Occator/DripMatic/src/ff.c

/*----------------------------------------------------------------------------/
/  FatFs - Generic FAT Filesystem Module  R0.13b                              /
/-----------------------------------------------------------------------------/
/
/ Copyright (C) 2018, ChaN, all right reserved.
/
/ FatFs module is an open source software. Redistribution and use of FatFs in
/ source and binary forms, with or without modification, are permitted provided
/ that the following condition is met:
/
/ 1. Redistributions of source code must retain the above copyright notice,
/    this condition and the following disclaimer.
/
/ This software is provided by the copyright holder and contributors "AS IS"
/ and any warranties related to this software are DISCLAIMED.
/ The copyright owner or contributors be NOT LIABLE for any damages caused
/ by use of this software.
/
/----------------------------------------------------------------------------*/


#include "ff.h"			/* Declarations of FatFs API */
#include "diskio.h"		/* Declarations of device I/O functions */

/*--------------------------------------------------------------------------
own includings
/----------------------------------------------------------------------------*/
#include "rtc_3w.h"

/*--------------------------------------------------------------------------

   Module Private Definitions

---------------------------------------------------------------------------*/

#if FF_DEFINED != 63463	/* Revision ID */
#error Wrong include file (ff.h).
#endif

extern "C"
{

/* Character code support macros */
#define IsUpper(c)		((c) >= 'A' && (c) <= 'Z')
#define IsLower(c)		((c) >= 'a' && (c) <= 'z')
#define IsDigit(c)		((c) >= '0' && (c) <= '9')
#define IsSurrogate(c)	((c) >= 0xD800 && (c) <= 0xDFFF)
#define IsSurrogateH(c)	((c) >= 0xD800 && (c) <= 0xDBFF)
#define IsSurrogateL(c)	((c) >= 0xDC00 && (c) <= 0xDFFF)


/* Additional file attribute bits for internal use */
#define AM_VOL		0x08	/* Volume label */
#define AM_LFN		0x0F	/* LFN entry */
#define AM_MASK		0x3F	/* Mask of defined bits */


/* Additional file access control and file status flags for internal use */
#define FA_SEEKEND	0x20	/* Seek to end of the file on file open */
#define FA_MODIFIED	0x40	/* File has been modified */
#define FA_DIRTY	0x80	/* FIL.buf[] needs to be written-back */


/* Name status flags in fn[11] */
#define NSFLAG		11		/* Index of the name status byte */
#define NS_LOSS		0x01	/* Out of 8.3 format */
#define NS_LFN		0x02	/* Force to create LFN entry */
#define NS_LAST		0x04	/* Last segment */
#define NS_BODY		0x08	/* Lower case flag (body) */
#define NS_EXT		0x10	/* Lower case flag (ext) */
#define NS_DOT		0x20	/* Dot entry */
#define NS_NOLFN	0x40	/* Do not find LFN */
#define NS_NONAME	0x80	/* Not followed */


/* Limits and boundaries */
#define MAX_DIR		0x200000		/* Max size of FAT directory */
#define MAX_DIR_EX	0x10000000		/* Max size of exFAT directory */
#define MAX_FAT12	0xFF5			/* Max FAT12 clusters (differs from specs, but right for real DOS/Windows behavior) */
#define MAX_FAT16	0xFFF5			/* Max FAT16 clusters (differs from specs, but right for real DOS/Windows behavior) */
#define MAX_FAT32	0x0FFFFFF5		/* Max FAT32 clusters (not specified, practical limit) */
#define MAX_EXFAT	0x7FFFFFFD		/* Max exFAT clusters (differs from specs, implementation limit) */


/* FatFs refers the FAT structure as simple byte array instead of structure member
/ because the C structure is not binary compatible between different platforms */

#define BS_JmpBoot			0		/* x86 jump instruction (3-byte) */
#define BS_OEMName			3		/* OEM name (8-byte) */
#define BPB_BytsPerSec		11		/* Sector size [byte] (WORD) */
#define BPB_SecPerClus		13		/* Cluster size [sector] (BYTE) */
#define BPB_RsvdSecCnt		14		/* Size of reserved area [sector] (WORD) */
#define BPB_NumFATs			16		/* Number of FATs (BYTE) */
#define BPB_RootEntCnt		17		/* Size of root directory area for FAT [entry] (WORD) */
#define BPB_TotSec16		19		/* Volume size (16-bit) [sector] (WORD) */
#define BPB_Media			21		/* Media descriptor byte (BYTE) */
#define BPB_FATSz16			22		/* FAT size (16-bit) [sector] (WORD) */
#define BPB_SecPerTrk		24		/* Number of sectors per track for int13h [sector] (WORD) */
#define BPB_NumHeads		26		/* Number of heads for int13h (WORD) */
#define BPB_HiddSec			28		/* Volume offset from top of the drive (DWORD) */
#define BPB_TotSec32		32		/* Volume size (32-bit) [sector] (DWORD) */
#define BS_DrvNum			36		/* Physical drive number for int13h (BYTE) */
#define BS_NTres			37		/* WindowsNT error flag (BYTE) */
#define BS_BootSig			38		/* Extended boot signature (BYTE) */
#define BS_VolID			39		/* Volume serial number (DWORD) */
#define BS_VolLab			43		/* Volume label string (8-byte) */
#define BS_FilSysType		54		/* Filesystem type string (8-byte) */
#define BS_BootCode			62		/* Boot code (448-byte) */
#define BS_55AA				510		/* Signature word (WORD) */

#define BPB_FATSz32			36		/* FAT32: FAT size [sector] (DWORD) */
#define BPB_ExtFlags32		40		/* FAT32: Extended flags (WORD) */
#define BPB_FSVer32			42		/* FAT32: Filesystem version (WORD) */
#define BPB_RootClus32		44		/* FAT32: Root directory cluster (DWORD) */
#define BPB_FSInfo32		48		/* FAT32: Offset of FSINFO sector (WORD) */
#define BPB_BkBootSec32		50		/* FAT32: Offset of backup boot sector (WORD) */
#define BS_DrvNum32			64		/* FAT32: Physical drive number for int13h (BYTE) */
#define BS_NTres32			65		/* FAT32: Error flag (BYTE) */
#define BS_BootSig32		66		/* FAT32: Extended boot signature (BYTE) */
#define BS_VolID32			67		/* FAT32: Volume serial number (DWORD) */
#define BS_VolLab32			71		/* FAT32: Volume label string (8-byte) */
#define BS_FilSysType32		82		/* FAT32: Filesystem type string (8-byte) */
#define BS_BootCode32		90		/* FAT32: Boot code (420-byte) */

#define BPB_ZeroedEx		11		/* exFAT: MBZ field (53-byte) */
#define BPB_VolOfsEx		64		/* exFAT: Volume offset from top of the drive [sector] (QWORD) */
#define BPB_TotSecEx		72		/* exFAT: Volume size [sector] (QWORD) */
#define BPB_FatOfsEx		80		/* exFAT: FAT offset from top of the volume [sector] (DWORD) */
#define BPB_FatSzEx			84		/* exFAT: FAT size [sector] (DWORD) */
#define BPB_DataOfsEx		88		/* exFAT: Data offset from top of the volume [sector] (DWORD) */
#define BPB_NumClusEx		92		/* exFAT: Number of clusters (DWORD) */
#define BPB_RootClusEx		96		/* exFAT: Root directory start cluster (DWORD) */
#define BPB_VolIDEx			100		/* exFAT: Volume serial number (DWORD) */
#define BPB_FSVerEx			104		/* exFAT: Filesystem version (WORD) */
#define BPB_VolFlagEx		106		/* exFAT: Volume flags (WORD) */
#define BPB_BytsPerSecEx	108		/* exFAT: Log2 of sector size in unit of byte (BYTE) */
#define BPB_SecPerClusEx	109		/* exFAT: Log2 of cluster size in unit of sector (BYTE) */
#define BPB_NumFATsEx		110		/* exFAT: Number of FATs (BYTE) */
#define BPB_DrvNumEx		111		/* exFAT: Physical drive number for int13h (BYTE) */
#define BPB_PercInUseEx		112		/* exFAT: Percent in use (BYTE) */
#define BPB_RsvdEx			113		/* exFAT: Reserved (7-byte) */
#define BS_BootCodeEx		120		/* exFAT: Boot code (390-byte) */

#define DIR_Name			0		/* Short file name (11-byte) */
#define DIR_Attr			11		/* Attribute (BYTE) */
#define DIR_NTres			12		/* Lower case flag (BYTE) */
#define DIR_CrtTime10		13		/* Created time sub-second (BYTE) */
#define DIR_CrtTime			14		/* Created time (DWORD) */
#define DIR_LstAccDate		18		/* Last accessed date (WORD) */
#define DIR_FstClusHI		20		/* Higher 16-bit of first cluster (WORD) */
#define DIR_ModTime			22		/* Modified time (DWORD) */
#define DIR_FstClusLO		26		/* Lower 16-bit of first cluster (WORD) */
#define DIR_FileSize		28		/* File size (DWORD) */
#define LDIR_Ord			0		/* LFN: LFN order and LLE flag (BYTE) */
#define LDIR_Attr			11		/* LFN: LFN attribute (BYTE) */
#define LDIR_Type			12		/* LFN: Entry type (BYTE) */
#define LDIR_Chksum			13		/* LFN: Checksum of the SFN (BYTE) */
#define LDIR_FstClusLO		26		/* LFN: MBZ field (WORD) */
#define XDIR_Type			0		/* exFAT: Type of exFAT directory entry (BYTE) */
#define XDIR_NumLabel		1		/* exFAT: Number of volume label characters (BYTE) */
#define XDIR_Label			2		/* exFAT: Volume label (11-WORD) */
#define XDIR_CaseSum		4		/* exFAT: Sum of case conversion table (DWORD) */
#define XDIR_NumSec			1		/* exFAT: Number of secondary entries (BYTE) */
#define XDIR_SetSum			2		/* exFAT: Sum of the set of directory entries (WORD) */
#define XDIR_Attr			4		/* exFAT: File attribute (WORD) */
#define XDIR_CrtTime		8		/* exFAT: Created time (DWORD) */
#define XDIR_ModTime		12		/* exFAT: Modified time (DWORD) */
#define XDIR_AccTime		16		/* exFAT: Last accessed time (DWORD) */
#define XDIR_CrtTime10		20		/* exFAT: Created time subsecond (BYTE) */
#define XDIR_ModTime10		21		/* exFAT: Modified time subsecond (BYTE) */
#define XDIR_CrtTZ			22		/* exFAT: Created timezone (BYTE) */
#define XDIR_ModTZ			23		/* exFAT: Modified timezone (BYTE) */
#define XDIR_AccTZ			24		/* exFAT: Last accessed timezone (BYTE) */
#define XDIR_GenFlags		33		/* exFAT: General secondary flags (BYTE) */
#define XDIR_NumName		35		/* exFAT: Number of file name characters (BYTE) */
#define XDIR_NameHash		36		/* exFAT: Hash of file name (WORD) */
#define XDIR_ValidFileSize	40		/* exFAT: Valid file size (QWORD) */
#define XDIR_FstClus		52		/* exFAT: First cluster of the file data (DWORD) */
#define XDIR_FileSize		56		/* exFAT: File/Directory size (QWORD) */

#define SZDIRE				32		/* Size of a directory entry */
#define DDEM				0xE5	/* Deleted directory entry mark set to DIR_Name[0] */
#define RDDEM				0x05	/* Replacement of the character collides with DDEM */
#define LLEF				0x40	/* Last long entry flag in LDIR_Ord */

#define FSI_LeadSig			0		/* FAT32 FSI: Leading signature (DWORD) */
#define FSI_StrucSig		484		/* FAT32 FSI: Structure signature (DWORD) */
#define FSI_Free_Count		488		/* FAT32 FSI: Number of free clusters (DWORD) */
#define FSI_Nxt_Free		492		/* FAT32 FSI: Last allocated cluster (DWORD) */

#define MBR_Table			446		/* MBR: Offset of partition table in the MBR */
#define SZ_PTE				16		/* MBR: Size of a partition table entry */
#define PTE_Boot			0		/* MBR PTE: Boot indicator */
#define PTE_StHead			1		/* MBR PTE: Start head */
#define PTE_StSec			2		/* MBR PTE: Start sector */
#define PTE_StCyl			3		/* MBR PTE: Start cylinder */
#define PTE_System			4		/* MBR PTE: System ID */
#define PTE_EdHead			5		/* MBR PTE: End head */
#define PTE_EdSec			6		/* MBR PTE: End sector */
#define PTE_EdCyl			7		/* MBR PTE: End cylinder */
#define PTE_StLba			8		/* MBR PTE: Start in LBA */
#define PTE_SizLba			12		/* MBR PTE: Size in LBA */


/* Post process on fatal error in the file operations */
#define ABORT(fs, res)		{ fp->err = (BYTE)(res); LEAVE_FF(fs, res); }


/* Re-entrancy related */
#if FF_FS_REENTRANT
#if FF_USE_LFN == 1
#error Static LFN work area cannot be used at thread-safe configuration
#endif
#define LEAVE_FF(fs, res)	{ unlock_fs(fs, res); return res; }
#else
#define LEAVE_FF(fs, res)	return res
#endif


/* Definitions of volume - physical location conversion */
#if FF_MULTI_PARTITION
#define LD2PD(vol) VolToPart[vol].pd	/* Get physical drive number */
#define LD2PT(vol) VolToPart[vol].pt	/* Get partition index */
#else
#define LD2PD(vol) (BYTE)(vol)	/* Each logical drive is bound to the same physical drive number */
#define LD2PT(vol) 0			/* Find first valid partition or in SFD */
#endif


/* Definitions of sector size */
#if (FF_MAX_SS < FF_MIN_SS) || (FF_MAX_SS != 512 && FF_MAX_SS != 1024 && FF_MAX_SS != 2048 && FF_MAX_SS != 4096) || (FF_MIN_SS != 512 && FF_MIN_SS != 1024 && FF_MIN_SS != 2048 && FF_MIN_SS != 4096)
#error Wrong sector size configuration
#endif
#if FF_MAX_SS == FF_MIN_SS
#define SS(fs)	((UINT)FF_MAX_SS)	/* Fixed sector size */
#else
#define SS(fs)	((fs)->ssize)	/* Variable sector size */
#endif


/* Timestamp */
#if FF_FS_NORTC == 1
#if FF_NORTC_YEAR < 1980 || FF_NORTC_YEAR > 2107 || FF_NORTC_MON < 1 || FF_NORTC_MON > 12 || FF_NORTC_MDAY < 1 || FF_NORTC_MDAY > 31
#error Invalid FF_FS_NORTC settings
#endif
#define GET_FATTIME()	((DWORD)(FF_NORTC_YEAR - 1980) << 25 | (DWORD)FF_NORTC_MON << 21 | (DWORD)FF_NORTC_MDAY << 16)
#else
#define GET_FATTIME()	get_fattime()
#endif


/* File lock controls */
#if FF_FS_LOCK != 0
#if FF_FS_READONLY
#error FF_FS_LOCK must be 0 at read-only configuration
#endif
typedef struct {
	FATFS *fs;		/* Object ID 1, volume (NULL:blank entry) */
	DWORD clu;		/* Object ID 2, containing directory (0:root) */
	DWORD ofs;		/* Object ID 3, offset in the directory */
	WORD ctr;		/* Object open counter, 0:none, 0x01..0xFF:read mode open count, 0x100:write mode */
} FILESEM;
#endif


/* SBCS up-case tables (\x80-\xFF) */
#define TBL_CT437  {0x80,0x9A,0x45,0x41,0x8E,0x41,0x8F,0x80,0x45,0x45,0x45,0x49,0x49,0x49,0x8E,0x8F, \
					0x90,0x92,0x92,0x4F,0x99,0x4F,0x55,0x55,0x59,0x99,0x9A,0x9B,0x9C,0x9D,0x9E,0x9F, \
					0x41,0x49,0x4F,0x55,0xA5,0xA5,0xA6,0xA7,0xA8,0xA9,0xAA,0xAB,0xAC,0xAD,0xAE,0xAF, \
					0xB0,0xB1,0xB2,0xB3,0xB4,0xB5,0xB6,0xB7,0xB8,0xB9,0xBA,0xBB,0xBC,0xBD,0xBE,0xBF, \
					0xC0,0xC1,0xC2,0xC3,0xC4,0xC5,0xC6,0xC7,0xC8,0xC9,0xCA,0xCB,0xCC,0xCD,0xCE,0xCF, \
					0xD0,0xD1,0xD2,0xD3,0xD4,0xD5,0xD6,0xD7,0xD8,0xD9,0xDA,0xDB,0xDC,0xDD,0xDE,0xDF, \
					0xE0,0xE1,0xE2,0xE3,0xE4,0xE5,0xE6,0xE7,0xE8,0xE9,0xEA,0xEB,0xEC,0xED,0xEE,0xEF, \
					0xF0,0xF1,0xF2,0xF3,0xF4,0xF5,0xF6,0xF7,0xF8,0xF9,0xFA,0xFB,0xFC,0xFD,0xFE,0xFF}
#define TBL_CT720  {0x80,0x81,0x82,0x83,0x84,0x85,0x86,0x87,0x88,0x89,0x8A,0x8B,0x8C,0x8D,0x8E,0x8F, \
					0x90,0x91,0x92,0x93,0x94,0x95,0x96,0x97,0x98,0x99,0x9A,0x9B,0x9C,0x9D,0x9E,0x9F, \
					0xA0,0xA1,0xA2,0xA3,0xA4,0xA5,0xA6,0xA7,0xA8,0xA9,0xAA,0xAB,0xAC,0xAD,0xAE,0xAF, \
					0xB0,0xB1,0xB2,0xB3,0xB4,0xB5,0xB6,0xB7,0xB8,0xB9,0xBA,0xBB,0xBC,0xBD,0xBE,0xBF, \
					0xC0,0xC1,0xC2,0xC3,0xC4,0xC5,0xC6,0xC7,0xC8,0xC9,0xCA,0xCB,0xCC,0xCD,0xCE,0xCF, \
					0xD0,0xD1,0xD2,0xD3,0xD4,0xD5,0xD6,0xD7,0xD8,0xD9,0xDA,0xDB,0xDC,0xDD,0xDE,0xDF, \
					0xE0,0xE1,0xE2,0xE3,0xE4,0xE5,0xE6,0xE7,0xE8,0xE9,0xEA,0xEB,0xEC,0xED,0xEE,0xEF, \
					0xF0,0xF1,0xF2,0xF3,0xF4,0xF5,0xF6,0xF7,0xF8,0xF9,0xFA,0xFB,0xFC,0xFD,0xFE,0xFF}
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
#define TBL_CT869  {0x80,0x81,0x82,0x83,0x84,0x85,0x86,0x87,0x88,0x89,0x8A,0x8B,0x8C,0x8D,0x8E,0x8F, \
					0x90,0x91,0x92,0x93,0x94,0x95,0x96,0x97,0x98,0x99,0x9A,0x86,0x9C,0x8D,0x8F,0x90, \
					0x91,0x90,0x92,0x95,0xA4,0xA5,0xA6,0xA7,0xA8,0xA9,0xAA,0xAB,0xAC,0xAD,0xAE,0xAF, \
					0xB0,0xB1,0xB2,0xB3,0xB4,0xB5,0xB6,0xB7,0xB8,0xB9,0xBA,0xBB,0xBC,0xBD,0xBE,0xBF, \
					0xC0,0xC1,0xC2,0xC3,0xC4,0xC5,0xC6,0xC7,0xC8,0xC9,0xCA,0xCB,0xCC,0xCD,0xCE,0xCF, \
					0xD0,0xD1,0xD2,0xD3,0xD4,0xD5,0xA4,0xA5,0xA6,0xD9,0xDA,0xDB,0xDC,0xA7,0xA8,0xDF, \
					0xA9,0xAA,0xAC,0xAD,0xB5,0xB6,0xB7,0xB8,0xBD,0xBE,0xC6,0xC7,0xCF,0xCF,0xD0,0xEF, \
					0xF0,0xF1,0xD1,0xD2,0xD3,0xF5,0xD4,0xF7,0xF8,0xF9,0xD5,0x96,0x95,0x98,0xFE,0xFF}


/* DBCS code range |----- 1st byte -----|  |----------- 2nd byte -----------| */
#define TBL_DC932 {0x81, 0x9F, 0xE0, 0xFC, 0x40, 0x7E, 0x80, 0xFC, 0x00, 0x00}
#define TBL_DC936 {0x81, 0xFE, 0x00, 0x00, 0x40, 0x7E, 0x80, 0xFE, 0x00, 0x00}
#define TBL_DC949 {0x81, 0xFE, 0x00, 0x00, 0x41, 0x5A, 0x61, 0x7A, 0x81, 0xFE}
#define TBL_DC950 {0x81, 0xFE, 0x00, 0x00, 0x40, 0x7E, 0xA1, 0xFE, 0x00, 0x00}


/* Macros for table definitions */
#define MERGE_2STR(a, b) a ## b
#define MKCVTBL(hd, cp) MERGE_2STR(hd, cp)




/*--------------------------------------------------------------------------

   Module Private Work Area

---------------------------------------------------------------------------*/
/* Remark: Variables defined here without initial value shall be guaranteed
/  zero/null at start-up. If not, the linker option or start-up routine is
/  not compliance with C standard. */

/*--------------------------------*/
/* File/Volume controls           */
/*--------------------------------*/

#if FF_VOLUMES < 1 || FF_VOLUMES > 10
#error Wrong FF_VOLUMES setting
#endif
static FATFS* FatFs[FF_VOLUMES];	/* Pointer to the filesystem objects (logical drives) */
static WORD Fsid;					/* Filesystem mount ID */

#if FF_FS_RPATH != 0
static BYTE CurrVol;				/* Current drive */
#endif

#if FF_FS_LOCK != 0
static FILESEM Files[FF_FS_LOCK];	/* Open object lock semaphores */
#endif

#if FF_STR_VOLUME_ID
#ifdef FF_VOLUME_STRS
static const char* const VolumeStr[FF_VOLUMES] = {FF_VOLUME_STRS};	/* Pre-defined volume ID */
#endif
#endif


/*--------------------------------*/
/* LFN/Directory working buffer   */
/*--------------------------------*/

#if FF_USE_LFN == 0		/* Non-LFN configuration */
#if FF_FS_EXFAT
#error LFN must be enabled when enable exFAT
#endif
#define DEF_NAMBUF
#define INIT_NAMBUF(fs)
#define FREE_NAMBUF()
#define LEAVE_MKFS(res)	return res

#else					/* LFN configurations */
#if FF_MAX_LFN < 12 || FF_MAX_LFN > 255
#error Wrong setting of FF_MAX_LFN
#endif
#if FF_LFN_BUF < FF_SFN_BUF || FF_SFN_BUF < 12
#error Wrong setting of FF_LFN_BUF or FF_SFN_BUF
#endif
#if FF_LFN_UNICODE < 0 || FF_LFN_UNICODE > 3
#error Wrong setting of FF_LFN_UNICODE
#endif
static const BYTE LfnOfs[] = {1,3,5,7,9,14,16,18,20,22,24,28,30};	/* FAT: Offset of LFN characters in the directory entry */
#define MAXDIRB(nc)	((nc + 44U) / 15 * SZDIRE)	/* exFAT: Size of directory entry block scratchpad buffer needed for the name length */

#if FF_USE_LFN == 1		/* LFN enabled with static working buffer */
#if FF_FS_EXFAT
static BYTE	DirBuf[MAXDIRB(FF_MAX_LFN)];	/* Directory entry block scratchpad buffer */
#endif
static WCHAR LfnBuf[FF_MAX_LFN + 1];		/* LFN working buffer */
#define DEF_NAMBUF
#define INIT_NAMBUF(fs)
#define FREE_NAMBUF()
#define LEAVE_MKFS(res)	return res

#elif FF_USE_LFN == 2 	/* LFN enabled with dynamic working buffer on the stack */
#if FF_FS_EXFAT
#define DEF_NAMBUF		WCHAR lbuf[FF_MAX_LFN+1]; BYTE dbuf[MAXDIRB(FF_MAX_LFN)];	/* LFN working buffer and directory entry block scratchpad buffer */
#define INIT_NAMBUF(fs)	{ (fs)->lfnbuf = lbuf; (fs)->dirbuf = dbuf; }
#define FREE_NAMBUF()
#else
#define DEF_NAMBUF		WCHAR lbuf[FF_MAX_LFN+1];	/* LFN working buffer */
#define INIT_NAMBUF(fs)	{ (fs)->lfnbuf = lbuf; }
#define FREE_NAMBUF()
#endif
#define LEAVE_MKFS(res)	return res

#elif FF_USE_LFN == 3 	/* LFN enabled with dynamic working buffer on the heap */
#if FF_FS_EXFAT
#define DEF_NAMBUF		WCHAR *lfn;	/* Pointer to LFN working buffer and directory entry block scratchpad buffer */
#define INIT_NAMBUF(fs)	{ lfn = ff_memalloc((FF_MAX_LFN+1)*2 + MAXDIRB(FF_MAX_LFN)); if (!lfn) LEAVE_FF(fs, FR_NOT_ENOUGH_CORE); (fs)->lfnbuf = lfn; (fs)->dirbuf = (BYTE*)(lfn+FF_MAX_LFN+1); }
#define FREE_NAMBUF()	ff_memfree(lfn)
#else
#define DEF_NAMBUF		WCHAR *lfn;	/* Pointer to LFN working buffer */
#define INIT_NAMBUF(fs)	{ lfn = ff_memalloc((FF_MAX_LFN+1)*2); if (!lfn) LEAVE_FF(fs, FR_NOT_ENOUGH_CORE); (fs)->lfnbuf = lfn; }
#define FREE_NAMBUF()	ff_memfree(lfn)
#endif
#define LEAVE_MKFS(res)	{ if (!work) ff_memfree(buf); return res; }
#define MAX_MALLOC	0x8000	/* Must be >=FF_MAX_SS */

#else
#error Wrong setting of FF_USE_LFN

#endif	/* FF_USE_LFN == 1 */
#endif	/* FF_USE_LFN == 0 */



/*--------------------------------*/
/* Code conversion tables         */
/*--------------------------------*/

#if FF_CODE_PAGE == 0		/* Run-time code page configuration */
#define CODEPAGE CodePage
static WORD CodePage;	/* Current code page */
static const BYTE *ExCvt, *DbcTbl;	/* Pointer to current SBCS up-case table and DBCS code range table below */
static const BYTE Ct437[] = TBL_CT437;
static const BYTE Ct720[] = TBL_CT720;
static const BYTE Ct737[] = TBL_CT737;
static const BYTE Ct771[] = TBL_CT771;
static const BYTE Ct775[] = TBL_CT775;
static const BYTE Ct850[] = TBL_CT850;
static const BYTE Ct852[] = TBL_CT852;
static const BYTE Ct855[] = TBL_CT855;
static const BYTE Ct857[] = TBL_CT857;
static const BYTE Ct860[] = TBL_CT860;
static const BYTE Ct861[] = TBL_CT861;
static const BYTE Ct862[] = TBL_CT862;
static const BYTE Ct863[] = TBL_CT863;
static const BYTE Ct864[] = TBL_CT864;
static const BYTE Ct865[] = TBL_CT865;
static const BYTE Ct866[] = TBL_CT866;
static const BYTE Ct869[] = TBL_CT869;
static const BYTE Dc932[] = TBL_DC932;
static const BYTE Dc936[] = TBL_DC936;
static const BYTE Dc949[] = TBL_DC949;
static const BYTE Dc950[] = TBL_DC950;

#elif FF_CODE_PAGE < 900	/* Static code page configuration (SBCS) */
#define CODEPAGE FF_CODE_PAGE
static const BYTE ExCvt[] = MKCVTBL(TBL_CT, FF_CODE_PAGE);

#else					/* Static code page configuration (DBCS) */
#define CODEPAGE FF_CODE_PAGE
static const BYTE DbcTbl[] = MKCVTBL(TBL_DC, FF_CODE_PAGE);

#endif




/*--------------------------------------------------------------------------

   Module Private Functions

---------------------------------------------------------------------------*/

/*-----------------------------------------------------------------------*/
/* RTC-Module get_fattime implementation                       */
/*-----------------------------------------------------------------------*/
DWORD get_fattime()
{

	cDeviceRTC::GetInstance().update_rtcTime();
	return ( (DWORD)(cDeviceRTC::GetInstance().rtcTime.year - 1980) << 25)
					| ( (DWORD)cDeviceRTC::GetInstance().rtcTime.month << 21)
					| ( (DWORD)cDeviceRTC::GetInstance().rtcTime.date << 16)
					| ( (DWORD)(cDeviceRTC::GetInstance().rtcTime.hours - 2) << 11)
					| ( (DWORD)cDeviceRTC::GetInstance().rtcTime.minutes << 5)
					| ( (DWORD)cDeviceRTC::GetInstance().rtcTime.seconds >> 1);
}

/*-----------------------------------------------------------------------*/
/* Load/Store multi-byte word in the FAT structure                       */
/*-----------------------------------------------------------------------*/

static WORD ld_word (const BYTE* ptr)	/*	 Load a 2-byte little-endian word */
{
	WORD rv;

	rv = ptr[1];
	rv = rv << 8 | ptr[0];
	return rv;
}

static DWORD ld_dword (const BYTE* ptr)	/* Load a 4-byte little-endian word */
{
	DWORD rv;

	rv = ptr[3];
	rv = rv << 8 | ptr[2];
	rv = rv << 8 | ptr[1];
	rv = rv << 8 | ptr[0];
	return rv;
}

#if FF_FS_EXFAT
static QWORD ld_qword (const BYTE* ptr)	/* Load an 8-byte little-endian word */
{
	QWORD rv;

	rv = ptr[7];
	rv = rv << 8 | ptr[6];
	rv = rv << 8 | ptr[5];
	rv = rv << 8 | ptr[4];
	rv = rv << 8 | ptr[3];
	rv = rv << 8 | ptr[2];
	rv = rv << 8 | ptr[1];
	rv = rv << 8 | ptr[0];
	return rv;
}
#endif

#if !FF_FS_READONLY
static void st_word (BYTE* ptr, WORD val)	/* Store a 2-byte word in little-endian */
{
	*ptr++ = (BYTE)val; val >>= 8;
	*ptr++ = (BYTE)val;
}

static void st_dword (BYTE* ptr, DWORD val)	/* Store a 4-byte word in little-endian */
{
	*ptr++ = (BYTE)val; val >>= 8;
	*ptr++ = (BYTE)val; val >>= 8;
	*ptr++ = (BYTE)val; val >>= 8;
	*ptr++ = (BYTE)val;
}

#if FF_FS_EXFAT
static void st_qword (BYTE* ptr, QWORD val)	/* Store an 8-byte word in little-endian */
{
	*ptr++ = (BYTE)val; val >>= 8;
	*ptr++ = (BYTE)val; val >>= 8;
	*ptr++ = (BYTE)val; val >>= 8;
	*ptr++ = (BYTE)val; val >>= 8;
	*ptr++ = (BYTE)val; val >>= 8;
	*ptr++ = (BYTE)val; val >>= 8;
	*ptr++ = (BYTE)val; val >>= 8;
	*ptr++ = (BYTE)val;
}
#endif
#endif	/* !FF_FS_READONLY */



/*-----------------------------------------------------------------------*/
/* String functions                                                      */
/*-----------------------------------------------------------------------*/

/* Copy memory to memory */
static void mem_cpy (void* dst, const void* src, UINT cnt)
{
	BYTE *d = (BYTE*)dst;
	const BYTE *s = (const BYTE*)src;

	if (cnt != 0) {
		do {
			*d++ = *s++;
		} while (--cnt);
	}
}


/* Fill memory block */
static void mem_set (void* dst, int val, UINT cnt)
{
	BYTE *d = (BYTE*)dst;

	do {
		*d++ = (BYTE)val;
	} while (--cnt);
}


/* Compare memory block */
static int mem_cmp (const void* dst, const void* src, UINT cnt)	/* ZR:same, NZ:different */
{
	const BYTE *d = (const BYTE *)dst, *s = (const BYTE *)src;
	int r = 0;

	do {
		r = *d++ - *s++;
	} while (--cnt && r == 0);

	return r;
}


/* Check if chr is contained in the string */
static int chk_chr (const char* str, int chr)	/* NZ:contained, ZR:not contained */
{
	while (*str && *str != chr) str++;
	return *str;
}


/* Test if the character is DBC 1st byte */
static int dbc_1st (BYTE c)
{
#if FF_CODE_PAGE == 0		/* Variable code page */
	if (DbcTbl && c >= DbcTbl[0]) {
		if (c <= DbcTbl[1]) return 1;					/* 1st byte range 1 */
		if (c >= DbcTbl[2] && c <= DbcTbl[3]) return 1;	/* 1st byte range 2 */
	}
#elif FF_CODE_PAGE >= 900	/* DBCS fixed code page */
	if (c >= DbcTbl[0]) {
		if (c <= DbcTbl[1]) return 1;
		if (c >= DbcTbl[2] && c <= DbcTbl[3]) return 1;
	}
#else						/* SBCS fixed code page */
	if (c != 0) return 0;	/* Always false */
#endif
	return 0;
}


/* Test if the character is DBC 2nd byte */
static int dbc_2nd (BYTE c)
{
#if FF_CODE_PAGE == 0		/* Variable code page */
	if (DbcTbl && c >= DbcTbl[4]) {
		if (c <= DbcTbl[5]) return 1;					/* 2nd byte range 1 */
		if (c >= DbcTbl[6] && c <= DbcTbl[7]) return 1;	/* 2nd byte range 2 */
		if (c >= DbcTbl[8] && c <= DbcTbl[9]) return 1;	/* 2nd byte range 3 */
	}
#elif FF_CODE_PAGE >= 900	/* DBCS fixed code page */
	if (c >= DbcTbl[4]) {
		if (c <= DbcTbl[5]) return 1;
		if (c >= DbcTbl[6] && c <= DbcTbl[7]) return 1;
		if (c >= DbcTbl[8] && c <= DbcTbl[9]) return 1;
	}
#else						/* SBCS fixed code page */
	if (c != 0) return 0;	/* Always false */
#endif
	return 0;
}


#if FF_USE_LFN

/* Get a character from TCHAR string in defined API encodeing */
static DWORD tchar2uni (	/* Returns character in UTF-16 encoding (>=0x10000 on double encoding unit, 0xFFFFFFFF on decode error) */
	const TCHAR** str		/* Pointer to pointer to TCHAR string in configured encoding */
)
{
	DWORD uc;
	const TCHAR *p = *str;

#if FF_LFN_UNICODE == 1		/* UTF-16 input */
	WCHAR wc;

	uc = *p++;	/* Get a unit */
	if (IsSurrogate(uc)) {	/* Surrogate? */
		wc = *p++;		/* Get low surrogate */
		if (!IsSurrogateH(uc) || !IsSurrogateL(wc)) return 0xFFFFFFFF;	/* Wrong surrogate? */
		uc = uc << 16 | wc;
	}

#elif FF_LFN_UNICODE == 2	/* UTF-8 input */
	BYTE b;
	int nf;

	uc = (BYTE)*p++;	/* Get a unit */
	if (uc & 0x80) {	/* Multiple byte code? */
		if ((uc & 0xE0) == 0xC0) {	/* 2-byte sequence? */
			uc &= 0x1F; nf = 1;
		} else {
			if ((uc & 0xF0) == 0xE0) {	/* 3-byte sequence? */
				uc &= 0x0F; nf = 2;
			} else {
				if ((uc & 0xF8) == 0xF0) {	/* 4-byte sequence? */
					uc &= 0x07; nf = 3;
				} else {					/* Wrong sequence */
					return 0xFFFFFFFF;
				}
			}
		}
		do {	/* Get trailing bytes */
			b = (BYTE)*p++;
			if ((b & 0xC0) != 0x80) return 0xFFFFFFFF;	/* Wrong sequence? */
			uc = uc << 6 | (b & 0x3F);
		} while (--nf != 0);
		if (uc < 0x80 || IsSurrogate(uc) || uc >= 0x110000) return 0xFFFFFFFF;	/* Wrong code? */
		if (uc >= 0x010000) uc = 0xD800DC00 | ((uc - 0x10000) << 6 & 0x3FF0000) | (uc & 0x3FF);	/* Make a surrogate pair if needed */
	}

#elif FF_LFN_UNICODE == 3	/* UTF-32 input */
	uc = (TCHAR)*p++;	/* Get a unit */
	if (uc >= 0x110000) return 0xFFFFFFFF;	/* Wrong code? */
	if (uc >= 0x010000) uc = 0xD800DC00 | ((uc - 0x10000) << 6 & 0x3FF0000) | (uc & 0x3FF);	/* Make a surrogate pair if needed */

#else		/* ANSI/OEM input */
	BYTE b;
	WCHAR wc;

	wc = (BYTE)*p++;			/* Get a byte */
	if (dbc_1st((BYTE)wc)) {	/* Is it a DBC 1st byte? */
		b = (BYTE)*p++;			/* Get 2nd byte */
		if (!dbc_2nd(b)) return 0xFFFFFFFF;	/* Invalid code? */
		wc = (wc << 8) + b;		/* Make a DBC */
	}
	if (wc != 0) {
		wc = ff_oem2uni(wc, CODEPAGE);	/* ANSI/OEM ==> Unicode */
		if (wc == 0) return 0xFFFFFFFF;	/* Invalid code? */
	}
	uc = wc;

#endif
	*str = p;	/* Next read pointer */
	return uc;
}


/* Output a TCHAR string in defined API encoding */
static BYTE put_utf (	/* Returns number of encoding units written (0:buffer overflow or wrong encoding) */
	DWORD chr,	/* UTF-16 encoded character (Double encoding unit char if >=0x10000) */
	TCHAR* buf,	/* Output buffer */
	UINT szb	/* Size of the buffer */
)
{
#if FF_LFN_UNICODE == 1	/* UTF-16 output */
	WCHAR hs, wc;

	hs = (WCHAR)(chr >> 16);
	wc = (WCHAR)chr;
	if (hs == 0) {	/* Single encoding unit? */
		if (szb < 1 || IsSurrogate(wc)) return 0;	/* Buffer overflow or wrong code? */
		*buf = wc;
		return 1;
	}
	if (szb < 2 || !IsSurrogateH(hs) || !IsSurrogateL(wc)) return 0;	/* Buffer overflow or wrong surrogate? */
	*buf++ = hs;
	*buf++ = wc;
	return 2;

#elif FF_LFN_UNICODE == 2	/* UTF-8 output */
	DWORD hc;

	if (chr < 0x80) {	/* Single byte code? */
		if (szb < 1) return 0;	/* Buffer overflow? */
		*buf = (TCHAR)chr;
		return 1;
	}
	if (chr < 0x800) {	/* 2-byte sequence? */
		if (szb < 2) return 0;	/* Buffer overflow? */
		*buf++ = (TCHAR)(0xC0 | (chr >> 6 & 0x1F));
		*buf++ = (TCHAR)(0x80 | (chr >> 0 & 0x3F));
		return 2;
	}
	if (chr < 0x10000) {	/* 3-byte sequence? */
		if (szb < 3 || IsSurrogate(chr)) return 0;	/* Buffer overflow or wrong code? */
		*buf++ = (TCHAR)(0xE0 | (chr >> 12 & 0x0F));
		*buf++ = (TCHAR)(0x80 | (chr >> 6 & 0x3F));
		*buf++ = (TCHAR)(0x80 | (chr >> 0 & 0x3F));
		return 3;
	}
	/* 4-byte sequence */
	if (szb < 4) return 0;	/* Buffer overflow? */
	hc = ((chr & 0xFFFF0000) - 0xD8000000) >> 6;	/* Get high 10 bits */
	chr = (chr & 0xFFFF) - 0xDC00;					/* Get low 10 bits */
	if (hc >= 0x100000 || chr >= 0x400) return 0;	/* Wrong surrogate? */
	chr = (hc | chr) + 0x10000;
	*buf++ = (TCHAR)(0xF0 | (chr >> 18 & 0x07));
	*buf++ = (TCHAR)(0x80 | (chr >> 12 & 0x3F));
	*buf++ = (TCHAR)(0x80 | (chr >> 6 & 0x3F));
	*buf++ = (TCHAR)(0x80 | (chr >> 0 & 0x3F));
	return 4;

#elif FF_LFN_UNICODE == 3	/* UTF-32 output */
	DWORD hc;

	if (szb < 1) return 0;	/* Buffer overflow? */
	if (chr >= 0x10000) {	/* Out of BMP? */
		hc = ((chr & 0xFFFF0000) - 0xD8000000) >> 6;	/* Get high 10 bits */
		chr = (chr & 0xFFFF) - 0xDC00;					/* Get low 10 bits */
		if (hc >= 0x100000 || chr >= 0x400) return 0;	/* Wrong surrogate? */
		chr = (hc | chr) + 0x10000;
	}
	*buf++ = (TCHAR)chr;
	return 1;

#else						/* ANSI/OEM output */
	WCHAR wc;

	wc = ff_uni2oem(chr, CODEPAGE);
	if (wc >= 0x100) {	/* Is this a DBC? */
		if (szb < 2) return 0;
		*buf++ = (char)(wc >> 8);	/* Store DBC 1st byte */
		*buf++ = (TCHAR)wc;			/* Store DBC 2nd byte */
		return 2;
	}
	if (wc == 0 || szb < 1) return 0;	/* Invalid char or buffer overflow? */
	*buf++ = (TCHAR)wc;					/* Store the character */
	return 1;
#endif
}
#endif	/* FF_USE_LFN */


#if FF_FS_REENTRANT
/*-----------------------------------------------------------------------*/
/* Request/Release grant to access the volume                            */
/*-----------------------------------------------------------------------*/
static int lock_fs (		/* 1:Ok, 0:timeout */
	FATFS* fs		/* Filesystem object */
)
{
	return ff_req_grant(fs->sobj);
}


static void unlock_fs (
	FATFS* fs,		/* Filesystem object */
	FRESULT res		/* Result code to be returned */
)
{
	if (fs && res != FR_NOT_ENABLED && res != FR_INVALID_DRIVE && res != FR_TIMEOUT) {
		ff_rel_grant(fs->sobj);
	}
}

#endif



#if FF_FS_LOCK != 0
/*-----------------------------------------------------------------------*/
/* File lock control functions                                           */
/*-----------------------------------------------------------------------*/

static FRESULT chk_lock (	/* Check if the file can be accessed */
	DIR* dp,		/* Directory object pointing the file to be checked */
	int acc			/* Desired access type (0:Read mode open, 1:Write mode open, 2:Delete or rename) */
)
{
	UINT i, be;

	/* Search open object table for the object */
	be = 0;
	for (i = 0; i < FF_FS_LOCK; i++) {
		if (Files[i].fs) {	/* Existing entry */
			if (Files[i].fs == dp->obj.fs &&	 	/* Check if the object matches with an open object */
				Files[i].clu == dp->obj.sclust &&
				Files[i].ofs == dp->dptr) break;
		} else {			/* Blank entry */
			be = 1;
		}
	}
	if (i == FF_FS_LOCK) {	/* The object has not been opened */
		return (!be && acc != 2) ? FR_TOO_MANY_OPEN_FILES : FR_OK;	/* Is there a blank entry for new object? */
	}

	/* The object was opened. Reject any open against writing file and all write mode open */
	return (acc != 0 || Files[i].ctr == 0x100) ? FR_LOCKED : FR_OK;
}


static int enq_lock (void)	/* Check if an entry is available for a new object */
{
	UINT i;

	for (i = 0; i < FF_FS_LOCK && Files[i].fs; i++) ;
	return (i == FF_FS_LOCK) ? 0 : 1;
}


static UINT inc_lock (	/* Increment object open counter and returns its index (0:Internal error) */
	DIR* dp,	/* Directory object pointing the file to register or increment */
	int acc		/* Desired access (0:Read, 1:Write, 2:Delete/Rename) */
)
{
	UINT i;


	for (i = 0; i < FF_FS_LOCK; i++) {	/* Find the object */
		if (Files[i].fs == dp->obj.fs &&
			Files[i].clu == dp->obj.sclust &&
			Files[i].ofs == dp->dptr) break;
	}

	if (i == FF_FS_LOCK) {				/* Not opened. Register it as new. */
		for (i = 0; i < FF_FS_LOCK && Files[i].fs; i++) ;
		if (i == FF_FS_LOCK) return 0;	/* No free entry to register (int err) */
		Files[i].fs = dp->obj.fs;
		Files[i].clu = dp->obj.sclust;
		Files[i].ofs = dp->dptr;
		Files[i].ctr = 0;
	}

	if (acc >= 1 && Files[i].ctr) return 0;	/* Access violation (int err) */

	Files[i].ctr = acc ? 0x100 : Files[i].ctr + 1;	/* Set semaphore value */

	return i + 1;	/* Index number origin from 1 */
}


static FRESULT dec_lock (	/* Decrement object open counter */
	UINT i			/* Semaphore index (1..) */
)
{
	WORD n;
	FRESULT res;


	if (--i < FF_FS_LOCK) {	/* Index number origin from 0 */
		n = Files[i].ctr;
		if (n == 0x100) n = 0;		/* If write mode open, delete the entry */
		if (n > 0) n--;				/* Decrement read mode open count */
		Files[i].ctr = n;
		if (n == 0) Files[i].fs = 0;	/* Delete the entry if open count gets zero */
		res = FR_OK;
	} else {
		res = FR_INT_ERR;			/* Invalid index nunber */
	}
	return res;
}


static void clear_lock (	/* Clear lock entries of the volume */
	FATFS *fs
)
{
	UINT i;

	for (i = 0; i < FF_FS_LOCK; i++) {
		if (Files[i].fs == fs) Files[i].fs = 0;
	}
}

#endif	/* FF_FS_LOCK != 0 */



/*-----------------------------------------------------------------------*/
/* Move/Flush disk access window in the filesystem object                */
/*-----------------------------------------------------------------------*/
#if !FF_FS_READONLY
static FRESULT sync_window (	/* Returns FR_OK or FR_DISK_ERR */
	FATFS* fs			/* Filesystem object */
)
{
	FRESULT res = FR_OK;


	if (fs->wflag) {	/* Is the disk access window dirty */
		if (disk_write(fs->pdrv, fs->win, fs->winsect, 1) == RES_OK) {	/* Write back the window */
			fs->wflag = 0;	/* Clear window dirty flag */
			if (fs->winsect - fs->fatbase < fs->fsize) {	/* Is it in the 1st FAT? */
				if (fs->n_fats == 2) disk_write(fs->pdrv, fs->win, fs->winsect + fs->fsize, 1);	/* Reflect it to 2nd FAT if needed */
			}
		} else {
			res = FR_DISK_ERR;
		}
	}
	return res;
}
#endif


static FRESULT move_window (	/* Returns FR_OK or FR_DISK_ERR */
	FATFS* fs,			/* Filesystem object */
	DWORD sector		/* Sector number to make appearance in the fs->win[] */
)
{
	FRESULT res = FR_OK;


	if (sector != fs->winsect) {	/* Window offset changed? */
#if !FF_FS_READONLY
		res = sync_window(fs);		/* Write-back changes */
#endif
		if (res == FR_OK) {			/* Fill sector window with new data */
			if (disk_read(fs->pdrv, fs->win, sector, 1) != RES_OK) {
				sector = 0xFFFFFFFF;	/* Invalidate window if read data is not valid */
				res = FR_DISK_ERR;
			}
			fs->winsect = sector;
		}
	}
	return res;
}




#if !FF_FS_READONLY
/*-----------------------------------------------------------------------*/
/* Synchronize filesystem and data on the storage                        */
/*-----------------------------------------------------------------------*/

static FRESULT sync_fs (	/* Returns FR_OK or FR_DISK_ERR */
	FATFS* fs		/* Filesystem object */
)
{
	FRESULT res;


	res = sync_window(fs);
	if (res == FR_OK) {
		if (fs->fs_type == FS_FAT32 && fs->fsi_flag == 1) {	/* FAT32: Update FSInfo sector if needed */
			/* Create FSInfo structure */
			mem_set(fs->win, 0, SS(fs));
			st_word(fs->win + BS_55AA, 0xAA55);
			st_dword(fs->win + FSI_LeadSig, 0x41615252);
			st_dword(fs->win + FSI_StrucSig, 0x61417272);
			st_dword(fs->win + FSI_Free_Count, fs->free_clst);
			st_dword(fs->win + FSI_Nxt_Free, fs->last_clst);
			/* Write it into the FSInfo sector */
			fs->winsect = fs->volbase + 1;
			disk_write(fs->pdrv, fs->win, fs->winsect, 1);
			fs->fsi_flag = 0;
		}
		/* Make sure that no pending write process in the lower layer */
		if (disk_ioctl(fs->pdrv, CTRL_SYNC, 0) != RES_OK) res = FR_DISK_ERR;
	}

	return res;
}

#endif



/*-----------------------------------------------------------------------*/
/* Get physical sector number from cluster number                        */
/*-----------------------------------------------------------------------*/

static DWORD clst2sect (	/* !=0:Sector number, 0:Failed (invalid cluster#) */
	FATFS* fs,		/* Filesystem object */
	DWORD clst		/* Cluster# to be converted */
)
{
	clst -= 2;		/* Cluster number is origin from 2 */
	if (clst >= fs->n_fatent - 2) return 0;		/* Is it invalid cluster number? */
	return fs->database + fs->csize * clst;		/* Start sector number of the cluster */
}




/*-----------------------------------------------------------------------*/
/* FAT access - Read value of a FAT entry                                */
/*-----------------------------------------------------------------------*/

static DWORD get_fat (		/* 0xFFFFFFFF:Disk error, 1:Internal error, 2..0x7FFFFFFF:Cluster status */
	FFOBJID* obj,	/* Corresponding object */
	DWORD clst		/* Cluster number to get the value */
)
{
	UINT wc, bc;
	DWORD val;
	FATFS *fs = obj->fs;


	if (clst < 2 || clst >= fs->n_fatent) {	/* Check if in valid range */
		val = 1;	/* Internal error */

	} else {
		val = 0xFFFFFFFF;	/* Default value falls on disk error */

		switch (fs->fs_type) {
		case FS_FAT12 :
			bc = (UINT)clst; bc += bc / 2;
			if (move_window(fs, fs->fatbase + (bc / SS(fs))) != FR_OK) break;
			wc = fs->win[bc++ % SS(fs)];		/* Get 1st byte of the entry */
			if (move_window(fs, fs->fatbase + (bc / SS(fs))) != FR_OK) break;
			wc |= fs->win[bc % SS(fs)] << 8;	/* Merge 2nd byte of the entry */
			val = (clst & 1) ? (wc >> 4) : (wc & 0xFFF);	/* Adjust bit position */
			break;

		case FS_FAT16 :
			if (move_window(fs, fs->fatbase + (clst / (SS(fs) / 2))) != FR_OK) break;
			val = ld_word(fs->win + clst * 2 % SS(fs));		/* Simple WORD array */
			break;

		case FS_FAT32 :
			if (move_window(fs, fs->fatbase + (clst / (SS(fs) / 4))) != FR_OK) break;
			val = ld_dword(fs->win + clst * 4 % SS(fs)) & 0x0FFFFFFF;	/* Simple DWORD array but mask out upper 4 bits */
			break;
#if FF_FS_EXFAT
		case FS_EXFAT :
			if ((obj->objsize != 0 && obj->sclust != 0) || obj->stat == 0) {	/* Object except root dir must have valid data length */
				DWORD cofs = clst - obj->sclust;	/* Offset from start cluster */
				DWORD clen = (DWORD)((obj->objsize - 1) / SS(fs)) / fs->csize;	/* Number of clusters - 1 */

				if (obj->stat == 2 && cofs <= clen) {	/* Is it a contiguous chain? */
					val = (cofs == clen) ? 0x7FFFFFFF : clst + 1;	/* No data on the FAT, generate the value */
					break;
				}
				if (obj->stat == 3 && cofs < obj->n_cont) {	/* Is it in the 1st fragment? */
					val = clst + 1; 	/* Generate the value */
					break;
				}
				if (obj->stat != 2) {	/* Get value from FAT if FAT chain is valid */
					if (obj->n_frag != 0) {	/* Is it on the growing edge? */
						val = 0x7FFFFFFF;	/* Generate EOC */
					} else {
						if (move_window(fs, fs->fatbase + (clst / (SS(fs) / 4))) != FR_OK) break;
						val = ld_dword(fs->win + clst * 4 % SS(fs)) & 0x7FFFFFFF;
					}
					break;
				}
			}
			/* go to default */
#endif
		default:
			val = 1;	/* Internal error */
		}
	}

	return val;
}




#if !FF_FS_READONLY
/*-----------------------------------------------------------------------*/
/* FAT access - Change value of a FAT entry                              */
/*-----------------------------------------------------------------------*/

static FRESULT put_fat (	/* FR_OK(0):succeeded, !=0:error */
	FATFS* fs,		/* Corresponding filesystem object */
	DWORD clst,		/* FAT index number (cluster number) to be changed */
	DWORD val		/* New value to be set to the entry */
)
{
	UINT bc;
	BYTE *p;
	FRESULT res = FR_INT_ERR;


	if (clst >= 2 && clst < fs->n_fatent) {	/* Check if in valid range */
		switch (fs->fs_type) {
		case FS_FAT12 :
			bc = (UINT)clst; bc += bc / 2;	/* bc: byte offset of the entry */
			res = move_window(fs, fs->fatbase + (bc / SS(fs)));
			if (res != FR_OK) break;
			p = fs->win + bc++ % SS(fs);
			*p = (clst & 1) ? ((*p & 0x0F) | ((BYTE)val << 4)) : (BYTE)val;		/* Put 1st byte */
			fs->wflag = 1;
			res = move_window(fs, fs->fatbase + (bc / SS(fs)));
			if (res != FR_OK) break;
			p = fs->win + bc % SS(fs);
			*p = (clst & 1) ? (BYTE)(val >> 4) : ((*p & 0xF0) | ((BYTE)(val >> 8) & 0x0F));	/* Put 2nd byte */
			fs->wflag = 1;
			break;

		case FS_FAT16 :
			res = move_window(fs, fs->fatbase + (clst / (SS(fs) / 2)));
			if (res != FR_OK) break;
			st_word(fs->win + clst * 2 % SS(fs), (WORD)val);	/* Simple WORD array */
			fs->wflag = 1;
			break;

		case FS_FAT32 :
#if FF_FS_EXFAT
		case FS_EXFAT :
#endif
			res = move_window(fs, fs->fatbase + (clst / (SS(fs) / 4)));
			if (res != FR_OK) break;
			if (!FF_FS_EXFAT || fs->fs_type != FS_EXFAT) {
				val = (val & 0x0FFFFFFF) | (ld_dword(fs->win + clst * 4 % SS(fs)) & 0xF0000000);
			}
			st_dword(fs->win + clst * 4 % SS(fs), val);
			fs->wflag = 1;
			break;
		}
	}
	return res;
}

#endif /* !FF_FS_READONLY */




#if FF_FS_EXFAT && !FF_FS_READONLY
/*-----------------------------------------------------------------------*/
/* exFAT: Accessing FAT and Allocation Bitmap                            */
/*-----------------------------------------------------------------------*/

/*--------------------------------------*/
/* Find a contiguous free cluster block */
/*--------------------------------------*/

static DWORD find_bitmap (	/* 0:Not found, 2..:Cluster block found, 0xFFFFFFFF:Disk error */
	FATFS* fs,	/* Filesystem object */
	DWORD clst,	/* Cluster number to scan from */
	DWORD ncl	/* Number of contiguous clusters to find (1..) */
)
{
	BYTE bm, bv;
	UINT i;
	DWORD val, scl, ctr;


	clst -= 2;	/* The first bit in the bitmap corresponds to cluster #2 */
	if (clst >= fs->n_fatent - 2) clst = 0;
	scl = val = clst; ctr = 0;
	for (;;) {
		if (move_window(fs, fs->database + val / 8 / SS(fs)) != FR_OK) return 0xFFFFFFFF;	/* (assuming bitmap is located top of the cluster heap) */
		i = val / 8 % SS(fs); bm = 1 << (val % 8);
		do {
			do {
				bv = fs->win[i] & bm; bm <<= 1;		/* Get bit value */
				if (++val >= fs->n_fatent - 2) {	/* Next cluster (with wrap-around) */
					val = 0; bm = 0; i = SS(fs);
				}
				if (bv == 0) {	/* Is it a free cluster? */
					if (++ctr == ncl) return scl + 2;	/* Check if run length is sufficient for required */
				} else {
					scl = val; ctr = 0;		/* Encountered a cluster in-use, restart to scan */
				}
				if (val == clst) return 0;	/* All cluster scanned? */
			} while (bm != 0);
			bm = 1;
		} while (++i < SS(fs));
	}
}


/*----------------------------------------*/
/* Set/Clear a block of allocation bitmap */
/*----------------------------------------*/

static FRESULT change_bitmap (
	FATFS* fs,	/* Filesystem object */
	DWORD clst,	/* Cluster number to change from */
	DWORD ncl,	/* Number of clusters to be changed */
	int bv		/* bit value to be set (0 or 1) */
)
{
	BYTE bm;
	UINT i;
	DWORD sect;


	clst -= 2;	/* The first bit corresponds to cluster #2 */
	sect = fs->database + clst / 8 / SS(fs);	/* Sector address (assuming bitmap is located top of the cluster heap) */
	i = clst / 8 % SS(fs);						/* Byte offset in the sector */
	bm = 1 << (clst % 8);						/* Bit mask in the byte */
	for (;;) {
		if (move_window(fs, sect++) != FR_OK) return FR_DISK_ERR;
		do {
			do {
				if (bv == (int)((fs->win[i] & bm) != 0)) return FR_INT_ERR;	/* Is the bit expected value? */
				fs->win[i] ^= bm;	/* Flip the bit */
				fs->wflag = 1;
				if (--ncl == 0) return FR_OK;	/* All bits processed? */
			} while (bm <<= 1);		/* Next bit */
			bm = 1;
		} while (++i < SS(fs));		/* Next byte */
		i = 0;
	}
}


/*---------------------------------------------*/
/* Fill the first fragment of the FAT chain    */
/*---------------------------------------------*/

static FRESULT fill_first_frag (
	FFOBJID* obj	/* Pointer to the corresponding object */
)
{
	FRESULT res;
	DWORD cl, n;


	if (obj->stat == 3) {	/* Has the object been changed 'fragmented' in this session? */
		for (cl = obj->sclust, n = obj->n_cont; n; cl++, n--) {	/* Create cluster chain on the FAT */
			res = put_fat(obj->fs, cl, cl + 1);
			if (res != FR_OK) return res;
		}
		obj->stat = 0;	/* Change status 'FAT chain is valid' */
	}
	return FR_OK;
}


/*---------------------------------------------*/
/* Fill the last fragment of the FAT chain     */
/*---------------------------------------------*/

static FRESULT fill_last_frag (
	FFOBJID* obj,	/* Pointer to the corresponding object */
	DWORD lcl,		/* Last cluster of the fragment */
	DWORD term		/* Value to set the last FAT entry */
)
{
	FRESULT res;


	while (obj->n_frag > 0) {	/* Create the chain of last fragment */
		res = put_fat(obj->fs, lcl - obj->n_frag + 1, (obj->n_frag > 1) ? lcl - obj->n_frag + 2 : term);
		if (res != FR_OK) return res;
		obj->n_frag--;
	}
	return FR_OK;
}

#endif	/* FF_FS_EXFAT && !FF_FS_READONLY */



#if !FF_FS_READONLY
/*-----------------------------------------------------------------------*/
/* FAT handling - Remove a cluster chain                                 */
/*-----------------------------------------------------------------------*/

static FRESULT remove_chain (	/* FR_OK(0):succeeded, !=0:error */
	FFOBJID* obj,		/* Corresponding object */
	DWORD clst,			/* Cluster to remove a chain from */
	DWORD pclst			/* Previous cluster of clst (0:entire chain) */
)
{
	FRESULT res = FR_OK;
	DWORD nxt;
	FATFS *fs = obj->fs;
#if FF_FS_EXFAT || FF_USE_TRIM
	DWORD scl = clst, ecl = clst;
#endif
#if FF_USE_TRIM
	DWORD rt[2];
#endif

	if (clst < 2 || clst >= fs->n_fatent) return FR_INT_ERR;	/* Check if in valid range */

	/* Mark the previous cluster 'EOC' on the FAT if it exists */
	if (pclst != 0 && (!FF_FS_EXFAT || fs->fs_type != FS_EXFAT || obj->stat != 2)) {
		res = put_fat(fs, pclst, 0xFFFFFFFF);
		if (res != FR_OK) return res;
	}

	/* Remove the chain */
	do {
		nxt = get_fat(obj, clst);			/* Get cluster status */
		if (nxt == 0) break;				/* Empty cluster? */
		if (nxt == 1) return FR_INT_ERR;	/* Internal error? */
		if (nxt == 0xFFFFFFFF) return FR_DISK_ERR;	/* Disk error? */
		if (!FF_FS_EXFAT || fs->fs_type != FS_EXFAT) {
			res = put_fat(fs, clst, 0);		/* Mark the cluster 'free' on the FAT */
			if (res != FR_OK) return res;
		}
		if (fs->free_clst < fs->n_fatent - 2) {	/* Update FSINFO */
			fs->free_clst++;
			fs->fsi_flag |= 1;
		}
#if FF_FS_EXFAT || FF_USE_TRIM
		if (ecl + 1 == nxt) {	/* Is next cluster contiguous? */
			ecl = nxt;
		} else {				/* End of contiguous cluster block */
#if FF_FS_EXFAT
			if (fs->fs_type == FS_EXFAT) {
				res = change_bitmap(fs, scl, ecl - scl + 1, 0);	/* Mark the cluster block 'free' on the bitmap */
				if (res != FR_OK) return res;
			}
#endif
#if FF_USE_TRIM
			rt[0] = clst2sect(fs, scl);					/* Start of data area freed */
			rt[1] = clst2sect(fs, ecl) + fs->csize - 1;	/* End of data area freed */
			disk_ioctl(fs->pdrv, CTRL_TRIM, rt);		/* Inform device the data in the block is no longer needed */
#endif
			scl = ecl = nxt;
		}
#endif
		clst = nxt;					/* Next cluster */
	} while (clst < fs->n_fatent);	/* Repeat while not the last link */

#if FF_FS_EXFAT
	/* Some post processes for chain status */
	if (fs->fs_type == FS_EXFAT) {
		if (pclst == 0) {	/* Has the entire chain been removed? */
			obj->stat = 0;		/* Change the chain status 'initial' */
		} else {
			if (obj->stat == 0) {	/* Is it a fragmented chain from the beginning of this session? */
				clst = obj->sclust;		/* Follow the chain to check if it gets contiguous */
				while (clst != pclst) {
					nxt = get_fat(obj, clst);
					if (nxt < 2) return FR_INT_ERR;
					if (nxt == 0xFFFFFFFF) return FR_DISK_ERR;
					if (nxt != clst + 1) break;	/* Not contiguous? */
					clst++;
				}
				if (clst == pclst) {	/* Has the chain got contiguous again? */
					obj->stat = 2;		/* Change the chain status 'contiguous' */
				}
			} else {
				if (obj->stat == 3 && pclst >= obj->sclust && pclst <= obj->sclust + obj->n_cont) {	/* Was the chain fragmented in this session and got contiguous again? */
					obj->stat = 2;	/* Change the chain status 'contiguous' */
				}
			}
		}
	}
#endif
	return FR_OK;
}




/*-----------------------------------------------------------------------*/
/* FAT handling - Stretch a chain or Create a new chain                  */
/*-----------------------------------------------------------------------*/

static DWORD create_chain (	/* 0:No free cluster, 1:Internal error, 0xFFFFFFFF:Disk error, >=2:New cluster# */
	FFOBJID* obj,		/* Corresponding object */
	DWORD clst			/* Cluster# to stretch, 0:Create a new chain */
)
{
	DWORD cs, ncl, scl;
	FRESULT res;
	FATFS *fs = obj->fs;


	if (clst == 0) {	/* Create a new chain */
		scl = fs->last_clst;				/* Suggested cluster to start to find */
		if (scl == 0 || scl >= fs->n_fatent) scl = 1;
	}
	else {				/* Stretch a chain */
		cs = get_fat(obj, clst);			/* Check the cluster status */
		if (cs < 2) return 1;				/* Test for insanity */
		if (cs == 0xFFFFFFFF) return cs;	/* Test for disk error */
		if (cs < fs->n_fatent) return cs;	/* It is already followed by next cluster */
		scl = clst;							/* Cluster to start to find */
	}
	if (fs->free_clst == 0) return 0;		/* No free cluster */

#if FF_FS_EXFAT
	if (fs->fs_type == FS_EXFAT) {	/* On the exFAT volume */
		ncl = find_bitmap(fs, scl, 1);				/* Find a free cluster */
		if (ncl == 0 || ncl == 0xFFFFFFFF) return ncl;	/* No free cluster or hard error? */
		res = change_bitmap(fs, ncl, 1, 1);			/* Mark the cluster 'in use' */
		if (res == FR_INT_ERR) return 1;
		if (res == FR_DISK_ERR) return 0xFFFFFFFF;
		if (clst == 0) {							/* Is it a new chain? */
			obj->stat = 2;							/* Set status 'contiguous' */
		} else {									/* It is a stretched chain */
			if (obj->stat == 2 && ncl != scl + 1) {	/* Is the chain got fragmented? */
				obj->n_cont = scl - obj->sclust;	/* Set size of the contiguous part */
				obj->stat = 3;						/* Change status 'just fragmented' */
			}
		}
		if (obj->stat != 2) {	/* Is the file non-contiguous? */
			if (ncl == clst + 1) {	/* Is the cluster next to previous one? */
				obj->n_frag = obj->n_frag ? obj->n_frag + 1 : 2;	/* Increment size of last framgent */
			} else {				/* New fragment */
				if (obj->n_frag == 0) obj->n_frag = 1;
				res = fill_last_frag(obj, clst, ncl);	/* Fill last fragment on the FAT and link it to new one */
				if (res == FR_OK) obj->n_frag = 1;
			}
		}
	} else
#endif
	{	/* On the FAT/FAT32 volume */
		ncl = 0;
		if (scl == clst) {						/* Stretching an existing chain? */
			ncl = scl + 1;						/* Test if next cluster is free */
			if (ncl >= fs->n_fatent) ncl = 2;
			cs = get_fat(obj, ncl);				/* Get next cluster status */
			if (cs == 1 || cs == 0xFFFFFFFF) return cs;	/* Test for error */
			if (cs != 0) {						/* Not free? */
				cs = fs->last_clst;				/* Start at suggested cluster if it is valid */
				if (cs >= 2 && cs < fs->n_fatent) scl = cs;
				ncl = 0;
			}
		}
		if (ncl == 0) {	/* The new cluster cannot be contiguous and find another fragment */
			ncl = scl;	/* Start cluster */
			for (;;) {
				ncl++;							/* Next cluster */
				if (ncl >= fs->n_fatent) {		/* Check wrap-around */
					ncl = 2;
					if (ncl > scl) return 0;	/* No free cluster found? */
				}
				cs = get_fat(obj, ncl);			/* Get the cluster status */
				if (cs == 0) break;				/* Found a free cluster? */
				if (cs == 1 || cs == 0xFFFFFFFF) return cs;	/* Test for error */
				if (ncl == scl) return 0;		/* No free cluster found? */
			}
		}
		res = put_fat(fs, ncl, 0xFFFFFFFF);		/* Mark the new cluster 'EOC' */
		if (res == FR_OK && clst != 0) {
			res = put_fat(fs, clst, ncl);		/* Link it from the previous one if needed */
		}
	}

	if (res == FR_OK) {			/* Update FSINFO if function succeeded. */
		fs->last_clst = ncl;
		if (fs->free_clst <= fs->n_fatent - 2) fs->free_clst--;
		fs->fsi_flag |= 1;
	} else {
		ncl = (res == FR_DISK_ERR) ? 0xFFFFFFFF : 1;	/* Failed. Generate error status */
	}

	return ncl;		/* Return new cluster number or error status */
}

#endif /* !FF_FS_READONLY */




#if FF_USE_FASTSEEK
/*-----------------------------------------------------------------------*/
/* FAT handling - Convert offset into cluster with link map table        */
/*-----------------------------------------------------------------------*/

static DWORD clmt_clust (	/* <2:Error, >=2:Cluster number */
	FIL* fp,		/* Pointer to the file object */
	FSIZE_t ofs		/* File offset to be converted to cluster# */
)
{
	DWORD cl, ncl, *tbl;
	FATFS *fs = fp->obj.fs;


	tbl = fp->cltbl + 1;	/* Top of CLMT */
	cl = (DWORD)(ofs / SS(fs) / fs->csize);	/* Cluster order from top of the file */
	for (;;) {
		ncl = *tbl++;			/* Number of cluters in the fragment */
		if (ncl == 0) return 0;	/* End of table? (error) */
		if (cl < ncl) break;	/* In this fragment? */
		cl -= ncl; tbl++;		/* Next fragment */
	}
	return cl + *tbl;	/* Return the cluster number */
}

#endif	/* FF_USE_FASTSEEK */




/*-----------------------------------------------------------------------*/
/* Directory handling - Fill a cluster with zeros                        */
/*-----------------------------------------------------------------------*/

#if !FF_FS_READONLY
static FRESULT dir_clear (	/* Returns FR_OK or FR_DISK_ERR */
	FATFS *fs,		/* Filesystem object */
	DWORD clst		/* Directory table to clear */
)
{
	DWORD sect;
	UINT n, szb;
	BYTE *ibuf;


	if (sync_window(fs) != FR_OK) return FR_DISK_ERR;	/* Flush disk access window */
	sect = clst2sect(fs, clst);		/* Top of the cluster */
	fs->winsect = sect;				/* Set window to top of the cluster */
	mem_set(fs->win, 0, SS(fs));	/* Clear window buffer */
#if FF_USE_LFN == 3		/* Quick table clear by using multi-secter write */
	/* Allocate a temporary buffer */
	for (szb = ((DWORD)fs->csize * SS(fs) >= MAX_MALLOC) ? MAX_MALLOC : fs->csize * SS(fs), ibuf = 0; szb > SS(fs) && (ibuf = ff_memalloc(szb)) == 0; szb /= 2) ;
	if (szb > SS(fs)) {		/* Buffer allocated? */
		mem_set(ibuf, 0, szb);
		szb /= SS(fs);		/* Bytes -> Sectors */
		for (n = 0; n < fs->csize && disk_write(fs->pdrv, ibuf, sect + n, szb) == RES_OK; n += szb) ;	/* Fill the cluster with 0 */
		ff_memfree(ibuf);
	} else
#endif
	{
		ibuf = fs->win; szb = 1;	/* Use window buffer (many single-sector writes may take a time) */
		for (n = 0; n < fs->csize && disk_write(fs->pdrv, ibuf, sect + n, szb) == RES_OK; n += szb) ;	/* Fill the cluster with 0 */
	}
	return (n == fs->csize) ? FR_OK : FR_DISK_ERR;
}
#endif	/* !FF_FS_READONLY */




/*-----------------------------------------------------------------------*/
/* Directory handling - Set directory index                              */
/*-----------------------------------------------------------------------*/

static FRESULT dir_sdi (	/* FR_OK(0):succeeded, !=0:error */
	DIR* dp,		/* Pointer to directory object */
	DWORD ofs		/* Offset of directory table */
)
{
	DWORD csz, clst;
	FATFS *fs = dp->obj.fs;


	if (ofs >= (DWORD)((FF_FS_EXFAT && fs->fs_type == FS_EXFAT) ? MAX_DIR_EX : MAX_DIR) || ofs % SZDIRE) {	/* Check range of offset and alignment */
		return FR_INT_ERR;
	}
	dp->dptr = ofs;				/* Set current offset */
	clst = dp->obj.sclust;		/* Table start cluster (0:root) */
	if (clst == 0 && fs->fs_type >= FS_FAT32) {	/* Replace cluster# 0 with root cluster# */
		clst = fs->dirbase;
		if (FF_FS_EXFAT) dp->obj.stat = 0;	/* exFAT: Root dir has an FAT chain */
	}

	if (clst == 0) {	/* Static table (root-directory on the FAT volume) */
		if (ofs / SZDIRE >= fs->n_rootdir) return FR_INT_ERR;	/* Is index out of range? */
		dp->sect = fs->dirbase;

	} else {			/* Dynamic table (sub-directory or root-directory on the FAT32/exFAT volume) */
		csz = (DWORD)fs->csize * SS(fs);	/* Bytes per cluster */
		while (ofs >= csz) {				/* Follow cluster chain */
			clst = get_fat(&dp->obj, clst);				/* Get next cluster */
			if (clst == 0xFFFFFFFF) return FR_DISK_ERR;	/* Disk error */
			if (clst < 2 || clst >= fs->n_fatent) return FR_INT_ERR;	/* Reached to end of table or internal error */
			ofs -= csz;
		}
		dp->sect = clst2sect(fs, clst);
	}
	dp->clust = clst;					/* Current cluster# */
	if (dp->sect == 0) return FR_INT_ERR;
	dp->sect += ofs / SS(fs);			/* Sector# of the directory entry */
	dp->dir = fs->win + (ofs % SS(fs));	/* Pointer to the entry in the win[] */

	return FR_OK;
}




/*-----------------------------------------------------------------------*/
/* Directory handling - Move directory table index next                  */
/*-----------------------------------------------------------------------*/

static FRESULT dir_next (	/* FR_OK(0):succeeded, FR_NO_FILE:End of table, FR_DENIED:Could not stretch */
	DIR* dp,				/* Pointer to the directory object */
	int stretch				/* 0: Do not stretch table, 1: Stretch table if needed */
)
{
	DWORD ofs, clst;
	FATFS *fs = dp->obj.fs;


	ofs = dp->dptr + SZDIRE;	/* Next entry */
	if (dp->sect == 0 || ofs >= (DWORD)((FF_FS_EXFAT && fs->fs_type == FS_EXFAT) ? MAX_DIR_EX : MAX_DIR)) return FR_NO_FILE;	/* Report EOT when offset has reached max value */

	if (ofs % SS(fs) == 0) {	/* Sector changed? */
		dp->sect++;				/* Next sector */

		if (dp->clust == 0) {	/* Static table */
			if (ofs / SZDIRE >= fs->n_rootdir) {	/* Report EOT if it reached end of static table */
				dp->sect = 0; return FR_NO_FILE;
			}
		}
		else {					/* Dynamic table */
			if ((ofs / SS(fs) & (fs->csize - 1)) == 0) {	/* Cluster changed? */
				clst = get_fat(&dp->obj, dp->clust);		/* Get next cluster */
				if (clst <= 1) return FR_INT_ERR;			/* Internal error */
				if (clst == 0xFFFFFFFF) return FR_DISK_ERR;	/* Disk error */
				if (clst >= fs->n_fatent) {					/* It reached end of dynamic table */
#if !FF_FS_READONLY
					if (!stretch) {								/* If no stretch, report EOT */
						dp->sect = 0; return FR_NO_FILE;
					}
					clst = create_chain(&dp->obj, dp->clust);	/* Allocate a cluster */
					if (clst == 0) return FR_DENIED;			/* No free cluster */
					if (clst == 1) return FR_INT_ERR;			/* Internal error */
					if (clst == 0xFFFFFFFF) return FR_DISK_ERR;	/* Disk error */
					if (dir_clear(fs, clst) != FR_OK) return FR_DISK_ERR;	/* Clean up the stretched table */
					if (FF_FS_EXFAT) dp->obj.stat |= 4;			/* exFAT: The directory has been stretched */
#else
					if (!stretch) dp->sect = 0;					/* (this line is to suppress compiler warning) */
					dp->sect = 0; return FR_NO_FILE;			/* Report EOT */
#endif
				}
				dp->clust = clst;		/* Initialize data for new cluster */
				dp->sect = clst2sect(fs, clst);
			}
		}
	}
	dp->dptr = ofs;						/* Current entry */
	dp->dir = fs->win + ofs % SS(fs);	/* Pointer to the entry in the win[] */

	return FR_OK;
}




#if !FF_FS_READONLY
/*-----------------------------------------------------------------------*/
/* Directory handling - Reserve a block of directory entries             */
/*-----------------------------------------------------------------------*/

static FRESULT dir_alloc (	/* FR_OK(0):succeeded, !=0:error */
	DIR* dp,				/* Pointer to the directory object */
	UINT nent				/* Number of contiguous entries to allocate */
)
{
	FRESULT res;
	UINT n;
	FATFS *fs = dp->obj.fs;


	res = dir_sdi(dp, 0);
	if (res == FR_OK) {
		n = 0;
		do {
			res = move_window(fs, dp->sect);
			if (res != FR_OK) break;
#if FF_FS_EXFAT
			if ((fs->fs_type == FS_EXFAT) ? (int)((dp->dir[XDIR_Type] & 0x80) == 0) : (int)(dp->dir[DIR_Name] == DDEM || dp->dir[DIR_Name] == 0)) {
#else
			if (dp->dir[DIR_Name] == DDEM || dp->dir[DIR_Name] == 0) {
#endif
				if (++n == nent) break;	/* A block of contiguous free entries is found */
			} else {
				n = 0;					/* Not a blank entry. Restart to search */
			}
			res = dir_next(dp, 1);
		} while (res == FR_OK);	/* Next entry with table stretch enabled */
	}

	if (res == FR_NO_FILE) res = FR_DENIED;	/* No directory entry to allocate */
	return res;
}

#endif	/* !FF_FS_READONLY */




/*-----------------------------------------------------------------------*/
/* FAT: Directory handling - Load/Store start cluster number             */
/*-----------------------------------------------------------------------*/

static DWORD ld_clust (	/* Returns the top cluster value of the SFN entry */
	FATFS* fs,			/* Pointer to the fs object */
	const BYTE* dir		/* Pointer to the key entry */
)
{
	DWORD cl;

	cl = ld_word(dir + DIR_FstClusLO);
	if (fs->fs_type == FS_FAT32) {
		cl |= (DWORD)ld_word(dir + DIR_FstClusHI) << 16;
	}

	return cl;
}


#if !FF_FS_READONLY
static void st_clust (
	FATFS* fs,	/* Pointer to the fs object */
	BYTE* dir,	/* Pointer to the key entry */
	DWORD cl	/* Value to be set */
)
{
	st_word(dir + DIR_FstClusLO, (WORD)cl);
	if (fs->fs_type == FS_FAT32) {
		st_word(dir + DIR_FstClusHI, (WORD)(cl >> 16));
	}
}
#endif



#if FF_USE_LFN
/*--------------------------------------------------------*/
/* FAT-LFN: Compare a part of file name with an LFN entry */
/*--------------------------------------------------------*/

static int cmp_lfn (		/* 1:matched, 0:not matched */
	const WCHAR* lfnbuf,	/* Pointer to the LFN working buffer to be compared */
	BYTE* dir				/* Pointer to the directory entry containing the part of LFN */
)
{
	UINT i, s;
	WCHAR wc, uc;


	if (ld_word(dir + LDIR_FstClusLO) != 0) return 0;	/* Check LDIR_FstClusLO */

	i = ((dir[LDIR_Ord] & 0x3F) - 1) * 13;	/* Offset in the LFN buffer */

	for (wc = 1, s = 0; s < 13; s++) {		/* Process all characters in the entry */
		uc = ld_word(dir + LfnOfs[s]);		/* Pick an LFN character */
		if (wc != 0) {
			if (i >= FF_MAX_LFN || ff_wtoupper(uc) != ff_wtoupper(lfnbuf[i++])) {	/* Compare it */
				return 0;					/* Not matched */
			}
			wc = uc;
		} else {
			if (uc != 0xFFFF) return 0;		/* Check filler */
		}
	}

	if ((dir[LDIR_Ord] & LLEF) && wc && lfnbuf[i]) return 0;	/* Last segment matched but different length */

	return 1;		/* The part of LFN matched */
}


#if FF_FS_MINIMIZE <= 1 || FF_FS_RPATH >= 2 || FF_USE_LABEL || FF_FS_EXFAT
/*-----------------------------------------------------*/
/* FAT-LFN: Pick a part of file name from an LFN entry */
/*-----------------------------------------------------*/

static int pick_lfn (	/* 1:succeeded, 0:buffer overflow or invalid LFN entry */
	WCHAR* lfnbuf,		/* Pointer to the LFN working buffer */
	BYTE* dir			/* Pointer to the LFN entry */
)
{
	UINT i, s;
	WCHAR wc, uc;


	if (ld_word(dir + LDIR_FstClusLO) != 0) return 0;	/* Check LDIR_FstClusLO is 0 */

	i = ((dir[LDIR_Ord] & ~LLEF) - 1) * 13;	/* Offset in the LFN buffer */

	for (wc = 1, s = 0; s < 13; s++) {		/* Process all characters in the entry */
		uc = ld_word(dir + LfnOfs[s]);		/* Pick an LFN character */
		if (wc != 0) {
			if (i >= FF_MAX_LFN) return 0;	/* Buffer overflow? */
			lfnbuf[i++] = wc = uc;			/* Store it */
		} else {
			if (uc != 0xFFFF) return 0;		/* Check filler */
		}
	}

	if (dir[LDIR_Ord] & LLEF) {				/* Put terminator if it is the last LFN part */
		if (i >= FF_MAX_LFN) return 0;		/* Buffer overflow? */
		lfnbuf[i] = 0;
	}

	return 1;		/* The part of LFN is valid */
}
#endif


#if !FF_FS_READONLY
/*-----------------------------------------*/
/* FAT-LFN: Create an entry of LFN entries */
/*-----------------------------------------*/

static void put_lfn (
	const WCHAR* lfn,	/* Pointer to the LFN */
	BYTE* dir,			/* Pointer to the LFN entry to be created */
	BYTE ord,			/* LFN order (1-20) */
	BYTE sum			/* Checksum of the corresponding SFN */
)
{
	UINT i, s;
	WCHAR wc;


	dir[LDIR_Chksum] = sum;			/* Set checksum */
	dir[LDIR_Attr] = AM_LFN;		/* Set attribute. LFN entry */
	dir[LDIR_Type] = 0;
	st_word(dir + LDIR_FstClusLO, 0);

	i = (ord - 1) * 13;				/* Get offset in the LFN working buffer */
	s = wc = 0;
	do {
		if (wc != 0xFFFF) wc = lfn[i++];	/* Get an effective character */
		st_word(dir + LfnOfs[s], wc);		/* Put it */
		if (wc == 0) wc = 0xFFFF;		/* Padding characters for left locations */
	} while (++s < 13);
	if (wc == 0xFFFF || !lfn[i]) ord |= LLEF;	/* Last LFN part is the start of LFN sequence */
	dir[LDIR_Ord] = ord;			/* Set the LFN order */
}

#endif	/* !FF_FS_READONLY */
#endif	/* FF_USE_LFN */



#if FF_USE_LFN && !FF_FS_READONLY
/*-----------------------------------------------------------------------*/
/* FAT-LFN: Create a Numbered SFN                                        */
/*-----------------------------------------------------------------------*/

static void gen_numname (
	BYTE* dst,			/* Pointer to the buffer to store numbered SFN */
	const BYTE* src,	/* Pointer to SFN */
	const WCHAR* lfn,	/* Pointer to LFN */
	UINT seq			/* Sequence number */
)
{
	BYTE ns[8], c;
	UINT i, j;
	WCHAR wc;
	DWORD sr;


	mem_cpy(dst, src, 11);

	if (seq > 5) {	/* In case of many collisions, generate a hash number instead of sequential number */
		sr = seq;
		while (*lfn) {	/* Create a CRC as hash value */
			wc = *lfn++;
			for (i = 0; i < 16; i++) {
				sr = (sr << 1) + (wc & 1);
				wc >>= 1;
				if (sr & 0x10000) sr ^= 0x11021;
			}
		}
		seq = (UINT)sr;
	}

	/* itoa (hexdecimal) */
	i = 7;
	do {
		c = (BYTE)((seq % 16) + '0');
		if (c > '9') c += 7;
		ns[i--] = c;
		seq /= 16;
	} while (seq);
	ns[i] = '~';

	/* Append the number to the SFN body */
	for (j = 0; j < i && dst[j] != ' '; j++) {
		if (dbc_1st(dst[j])) {
			if (j == i - 1) break;
			j++;
		}
	}
	do {
		dst[j++] = (i < 8) ? ns[i++] : ' ';
	} while (j < 8);
}
#endif	/* FF_USE_LFN && !FF_FS_READONLY */



#if FF_USE_LFN
/*-----------------------------------------------------------------------*/
/* FAT-LFN: Calculate checksum of an SFN entry                           */
/*-----------------------------------------------------------------------*/

static BYTE sum_sfn (
	const BYTE* dir		/* Pointer to the SFN entry */
)
{
	BYTE sum = 0;
	UINT n = 11;

	do {
		sum = (sum >> 1) + (sum << 7) + *dir++;
	} while (--n);
	return sum;
}

#endif	/* FF_USE_LFN */



#if FF_FS_EXFAT
/*-----------------------------------------------------------------------*/
/* exFAT: Checksum                                                       */
/*-----------------------------------------------------------------------*/

static WORD xdir_sum (	/* Get checksum of the directoly entry block */
	const BYTE* dir		/* Directory entry block to be calculated */
)
{
	UINT i, szblk;
	WORD sum;


	szblk = (dir[XDIR_NumSec] + 1) * SZDIRE;	/* Number of bytes of the entry block */
	for (i = sum = 0; i < szblk; i++) {
		if (i == XDIR_SetSum) {	/* Skip 2-byte sum field */
			i++;
		} else {
			sum = ((sum & 1) ? 0x8000 : 0) + (sum >> 1) + dir[i];
		}
	}
	return sum;
}



static WORD xname_sum (	/* Get check sum (to be used as hash) of the file name */
	const WCHAR* name	/* File name to be calculated */
)
{
	WCHAR chr;
	WORD sum = 0;


	while ((chr = *name++) != 0) {
		chr = (WCHAR)ff_wtoupper(chr);		/* File name needs to be up-case converted */
		sum = ((sum & 1) ? 0x8000 : 0) + (sum >> 1) + (chr & 0xFF);
		sum = ((sum & 1) ? 0x8000 : 0) + (sum >> 1) + (chr >> 8);
	}
	return sum;
}


#if !FF_FS_READONLY && FF_USE_MKFS
static DWORD xsum32 (	/* Returns 32-bit checksum */
	BYTE  dat,			/* Byte to be calculated (byte-by-byte processing) */
	DWORD sum			/* Previous sum value */
)
{
	sum = ((sum & 1) ? 0x80000000 : 0) + (sum >> 1) + dat;
	return sum;
}
#endif


#if FF_FS_MINIMIZE <= 1 || FF_FS_RPATH >= 2
/*------------------------------------------------------*/
/* exFAT: Get object information from a directory block */
/*------------------------------------------------------*/

static void get_xfileinfo (
	BYTE* dirb,			/* Pointer to the direcotry entry block 85+C0+C1s */
	FILINFO* fno		/* Buffer to store the extracted file information */
)
{
	WCHAR wc, hs;
	UINT di, si, nc;

	/* Get file name from the entry block */
	si = SZDIRE * 2;	/* 1st C1 entry */
	nc = 0; hs = 0; di = 0;
	while (nc < dirb[XDIR_NumName]) {
		if (si >= MAXDIRB(FF_MAX_LFN)) { di = 0; break; }	/* Truncated directory block? */
		if ((si % SZDIRE) == 0) si += 2;		/* Skip entry type field */
		wc = ld_word(dirb + si); si += 2; nc++;	/* Get a character */
		if (hs == 0 && IsSurrogate(wc)) {	/* Is it a surrogate? */
			hs = wc; continue;	/* Get low surrogate */
		}
		wc = put_utf((DWORD)hs << 16 | wc, &fno->fname[di], FF_LFN_BUF - di);	/* Store it in API encoding */
		if (wc == 0) { di = 0; break; }	/* Buffer overflow or wrong encoding? */
		di += wc;
		hs = 0;
	}
	if (hs != 0) di = 0;					/* Broken surrogate pair? */
	if (di == 0) fno->fname[di++] = '?';	/* Inaccessible object name? */
	fno->fname[di] = 0;						/* Terminate the name */
	fno->altname[0] = 0;					/* exFAT does not support SFN */

	fno->fattrib = dirb[XDIR_Attr];			/* Attribute */
	fno->fsize = (fno->fattrib & AM_DIR) ? 0 : ld_qword(dirb + XDIR_FileSize);	/* Size */
	fno->ftime = ld_word(dirb + XDIR_ModTime + 0);	/* Time */
	fno->fdate = ld_word(dirb + XDIR_ModTime + 2);	/* Date */
}

#endif	/* FF_FS_MINIMIZE <= 1 || FF_FS_RPATH >= 2 */


/*-----------------------------------*/
/* exFAT: Get a directry entry block */
/*-----------------------------------*/

static FRESULT load_xdir (	/* FR_INT_ERR: invalid entry block */
	DIR* dp					/* Reading direcotry object pointing top of the entry block to load */
)
{
	FRESULT res;
	UINT i, sz_ent;
	BYTE* dirb = dp->obj.fs->dirbuf;	/* Pointer to the on-memory direcotry entry block 85+C0+C1s */


	/* Load 85 entry */
	res = move_window(dp->obj.fs, dp->sect);
	if (res != FR_OK) return res;
	if (dp->dir[XDIR_Type] != 0x85) return FR_INT_ERR;	/* Invalid order */
	mem_cpy(dirb + 0 * SZDIRE, dp->dir, SZDIRE);
	sz_ent = (dirb[XDIR_NumSec] + 1) * SZDIRE;
	if (sz_ent < 3 * SZDIRE || sz_ent > 19 * SZDIRE) return FR_INT_ERR;

	/* Load C0 entry */
	res = dir_next(dp, 0);
	if (res == FR_NO_FILE) res = FR_INT_ERR;	/* It cannot be */
	if (res != FR_OK) return res;
	res = move_window(dp->obj.fs, dp->sect);
	if (res != FR_OK) return res;
	if (dp->dir[XDIR_Type] != 0xC0) return FR_INT_ERR;	/* Invalid order */
	mem_cpy(dirb + 1 * SZDIRE, dp->dir, SZDIRE);
	if (MAXDIRB(dirb[XDIR_NumName]) > sz_ent) return FR_INT_ERR;

	/* Load C1 entries */
	i = 2 * SZDIRE;	/* C1 offset to load */
	do {
		res = dir_next(dp, 0);
		if (res == FR_NO_FILE) res = FR_INT_ERR;	/* It cannot be */
		if (res != FR_OK) return res;
		res = move_window(dp->obj.fs, dp->sect);
		if (res != FR_OK) return res;
		if (dp->dir[XDIR_Type] != 0xC1) return FR_INT_ERR;	/* Invalid order */
		if (i < MAXDIRB(FF_MAX_LFN)) mem_cpy(dirb + i, dp->dir, SZDIRE);
	} while ((i += SZDIRE) < sz_ent);

	/* Sanity check (do it for only accessible object) */
	if (i <= MAXDIRB(FF_MAX_LFN)) {
		if (xdir_sum(dirb) != ld_word(dirb + XDIR_SetSum)) return FR_INT_ERR;
	}
	return FR_OK;
}


/*------------------------------------------------------------------*/
/* exFAT: Initialize object allocation info with loaded entry block */
/*------------------------------------------------------------------*/

static void init_alloc_info (
	FATFS* fs,		/* Filesystem object */
	FFOBJID* obj	/* Object allocation information to be initialized */
)
{
	obj->sclust = ld_dword(fs->dirbuf + XDIR_FstClus);		/* Start cluster */
	obj->objsize = ld_qword(fs->dirbuf + XDIR_FileSize);	/* Size */
	obj->stat = fs->dirbuf[XDIR_GenFlags] & 2;				/* Allocation status */
	obj->n_frag = 0;										/* No last fragment info */
}



#if !FF_FS_READONLY || FF_FS_RPATH != 0
/*------------------------------------------------*/
/* exFAT: Load the object's directory entry block */
/*------------------------------------------------*/

static FRESULT load_obj_xdir (
	DIR* dp,			/* Blank directory object to be used to access containing direcotry */
	const FFOBJID* obj	/* Object with its containing directory information */
)
{
	FRESULT res;

	/* Open object containing directory */
	dp->obj.fs = obj->fs;
	dp->obj.sclust = obj->c_scl;
	dp->obj.stat = (BYTE)obj->c_size;
	dp->obj.objsize = obj->c_size & 0xFFFFFF00;
	dp->obj.n_frag = 0;
	dp->blk_ofs = obj->c_ofs;

	res = dir_sdi(dp, dp->blk_ofs);	/* Goto object's entry block */
	if (res == FR_OK) {
		res = load_xdir(dp);		/* Load the object's entry block */
	}
	return res;
}
#endif


#if !FF_FS_READONLY
/*----------------------------------------*/
/* exFAT: Store the directory entry block */
/*----------------------------------------*/

static FRESULT store_xdir (
	DIR* dp				/* Pointer to the direcotry object */
)
{
	FRESULT res;
	UINT nent;
	BYTE* dirb = dp->obj.fs->dirbuf;	/* Pointer to the direcotry entry block 85+C0+C1s */

	/* Create set sum */
	st_word(dirb + XDIR_SetSum, xdir_sum(dirb));
	nent = dirb[XDIR_NumSec] + 1;

	/* Store the direcotry entry block to the directory */
	res = dir_sdi(dp, dp->blk_ofs);
	while (res == FR_OK) {
		res = move_window(dp->obj.fs, dp->sect);
		if (res != FR_OK) break;
		mem_cpy(dp->dir, dirb, SZDIRE);
		dp->obj.fs->wflag = 1;
		if (--nent == 0) break;
		dirb += SZDIRE;
		res = dir_next(dp, 0);
	}
	return (res == FR_OK || res == FR_DISK_ERR) ? res : FR_INT_ERR;
}



/*-------------------------------------------*/
/* exFAT: Create a new directory enrty block */
/*-------------------------------------------*/

static void create_xdir (
	BYTE* dirb,			/* Pointer to the direcotry entry block buffer */
	const WCHAR* lfn	/* Pointer to the object name */
)
{
	UINT i;
	BYTE nc1, nlen;
	WCHAR wc;


	/* Create 85,C0 entry */
	mem_set(dirb, 0, 2 * SZDIRE);
	dirb[0 * SZDIRE + XDIR_Type] = 0x85;	/* 85 entry */
	dirb[1 * SZDIRE + XDIR_Type] = 0xC0;	/* C0 entry */

	/* Create C1 entries */
	i = SZDIRE * 2;	/* Top of C1 entries */
	nlen = nc1 = 0; wc = 1;
	do {
		dirb[i++] = 0xC1; dirb[i++] = 0;	/* Entry type C1 */
		do {	/* Fill name field */
			if (wc != 0 && (wc = lfn[nlen]) != 0) nlen++;	/* Get a character if exist */
			st_word(dirb + i, wc); 		/* Store it */
			i += 2;
		} while (i % SZDIRE != 0);
		nc1++;
	} while (lfn[nlen]);	/* Fill next entry if any char follows */

	dirb[XDIR_NumName] = nlen;		/* Set name length */
	dirb[XDIR_NumSec] = 1 + nc1;	/* Set secondary count (C0 + C1s) */
	st_word(dirb + XDIR_NameHash, xname_sum(lfn));	/* Set name hash */
}

#endif	/* !FF_FS_READONLY */
#endif	/* FF_FS_EXFAT */



#if FF_FS_MINIMIZE <= 1 || FF_FS_RPATH >= 2 || FF_USE_LABEL || FF_FS_EXFAT
/*-----------------------------------------------------------------------*/
/* Read an object from the directory                                     */
/*-----------------------------------------------------------------------*/

#define dir_read_file(dp) dir_read(dp, 0)
#define dir_read_label(dp) dir_read(dp, 1)

static FRESULT dir_read (
	DIR* dp,		/* Pointer to the directory object */
	int vol			/* Filtered by 0:file/directory or 1:volume label */
)
{
	FRESULT res = FR_NO_FILE;
	FATFS *fs = dp->obj.fs;
	BYTE a, c;
#if FF_USE_LFN
	BYTE ord = 0xFF, sum = 0xFF;
#endif

	while (dp->sect) {
		res = move_window(fs, dp->sect);
		if (res != FR_OK) break;
		c = dp->dir[DIR_Name];	/* Test for the entry type */
		if (c == 0) {
			res = FR_NO_FILE; break; /* Reached to end of the directory */
		}
#if FF_FS_EXFAT
		if (fs->fs_type == FS_EXFAT) {	/* On the exFAT volume */
			if (FF_USE_LABEL && vol) {
				if (c == 0x83) break;	/* Volume label entry? */
			} else {
				if (c == 0x85) {		/* Start of the file entry block? */
					dp->blk_ofs = dp->dptr;	/* Get location of the block */
					res = load_xdir(dp);	/* Load the entry block */
					if (res == FR_OK) {
						dp->obj.attr = fs->dirbuf[XDIR_Attr] & AM_MASK;	/* Get attribute */
					}
					break;
				}
			}
		} else
#endif
		{	/* On the FAT/FAT32 volume */
			dp->obj.attr = a = dp->dir[DIR_Attr] & AM_MASK;	/* Get attribute */
#if FF_USE_LFN		/* LFN configuration */
			if (c == DDEM || c == '.' || (int)((a & ~AM_ARC) == AM_VOL) != vol) {	/* An entry without valid data */
				ord = 0xFF;
			} else {
				if (a == AM_LFN) {			/* An LFN entry is found */
					if (c & LLEF) {			/* Is it start of an LFN sequence? */
						sum = dp->dir[LDIR_Chksum];
						c &= (BYTE)~LLEF; ord = c;
						dp->blk_ofs = dp->dptr;
					}
					/* Check LFN validity and capture it */
					ord = (c == ord && sum == dp->dir[LDIR_Chksum] && pick_lfn(fs->lfnbuf, dp->dir)) ? ord - 1 : 0xFF;
				} else {					/* An SFN entry is found */
					if (ord != 0 || sum != sum_sfn(dp->dir)) {	/* Is there a valid LFN? */
						dp->blk_ofs = 0xFFFFFFFF;			/* It has no LFN. */
					}
					break;
				}
			}
#else		/* Non LFN configuration */
			if (c != DDEM && c != '.' && a != AM_LFN && (int)((a & ~AM_ARC) == AM_VOL) == vol) {	/* Is it a valid entry? */
				break;
			}
#endif
		}
		res = dir_next(dp, 0);		/* Next entry */
		if (res != FR_OK) break;
	}

	if (res != FR_OK) dp->sect = 0;		/* Terminate the read operation on error or EOT */
	return res;
}

#endif	/* FF_FS_MINIMIZE <= 1 || FF_USE_LABEL || FF_FS_RPATH >= 2 */



/*-----------------------------------------------------------------------*/
/* Directory handling - Find an object in the directory                  */
/*-----------------------------------------------------------------------*/

static FRESULT dir_find (	/* FR_OK(0):succeeded, !=0:error */
	DIR* dp					/* Pointer to the directory object with the file name */
)
{
	FRESULT res;
	FATFS *fs = dp->obj.fs;
	BYTE c;
#if FF_USE_LFN
	BYTE a, ord, sum;
#endif

	res = dir_sdi(dp, 0);			/* Rewind directory object */
	if (res != FR_OK) return res;
#if FF_FS_EXFAT
	if (fs->fs_type == FS_EXFAT) {	/* On the exFAT volume */
		BYTE nc;
		UINT di, ni;
		WORD hash = xname_sum(fs->lfnbuf);		/* Hash value of the name to find */

		while ((res = dir_read_file(dp)) == FR_OK) {	/* Read an item */
#if FF_MAX_LFN < 255
			if (fs->dirbuf[XDIR_NumName] > FF_MAX_LFN) continue;			/* Skip comparison if inaccessible object name */
#endif
			if (ld_word(fs->dirbuf + XDIR_NameHash) != hash) continue;	/* Skip comparison if hash mismatched */
			for (nc = fs->dirbuf[XDIR_NumName], di = SZDIRE * 2, ni = 0; nc; nc--, di += 2, ni++) {	/* Compare the name */
				if ((di % SZDIRE) == 0) di += 2;
				if (ff_wtoupper(ld_word(fs->dirbuf + di)) != ff_wtoupper(fs->lfnbuf[ni])) break;
			}
			if (nc == 0 && !fs->lfnbuf[ni]) break;	/* Name matched? */
		}
		return res;
	}
#endif
	/* On the FAT/FAT32 volume */
#if FF_USE_LFN
	ord = sum = 0xFF; dp->blk_ofs = 0xFFFFFFFF;	/* Reset LFN sequence */
#endif
	do {
		res = move_window(fs, dp->sect);
		if (res != FR_OK) break;
		c = dp->dir[DIR_Name];
		if (c == 0) { res = FR_NO_FILE; break; }	/* Reached to end of table */
#if FF_USE_LFN		/* LFN configuration */
		dp->obj.attr = a = dp->dir[DIR_Attr] & AM_MASK;
		if (c == DDEM || ((a & AM_VOL) && a != AM_LFN)) {	/* An entry without valid data */
			ord = 0xFF; dp->blk_ofs = 0xFFFFFFFF;	/* Reset LFN sequence */
		} else {
			if (a == AM_LFN) {			/* An LFN entry is found */
				if (!(dp->fn[NSFLAG] & NS_NOLFN)) {
					if (c & LLEF) {		/* Is it start of LFN sequence? */
						sum = dp->dir[LDIR_Chksum];
						c &= (BYTE)~LLEF; ord = c;	/* LFN start order */
						dp->blk_ofs = dp->dptr;	/* Start offset of LFN */
					}
					/* Check validity of the LFN entry and compare it with given name */
					ord = (c == ord && sum == dp->dir[LDIR_Chksum] && cmp_lfn(fs->lfnbuf, dp->dir)) ? ord - 1 : 0xFF;
				}
			} else {					/* An SFN entry is found */
				if (ord == 0 && sum == sum_sfn(dp->dir)) break;	/* LFN matched? */
				if (!(dp->fn[NSFLAG] & NS_LOSS) && !mem_cmp(dp->dir, dp->fn, 11)) break;	/* SFN matched? */
				ord = 0xFF; dp->blk_ofs = 0xFFFFFFFF;	/* Reset LFN sequence */
			}
		}
#else		/* Non LFN configuration */
		dp->obj.attr = dp->dir[DIR_Attr] & AM_MASK;
		if (!(dp->dir[DIR_Attr] & AM_VOL) && !mem_cmp(dp->dir, dp->fn, 11)) break;	/* Is it a valid entry? */
#endif
		res = dir_next(dp, 0);	/* Next entry */
	} while (res == FR_OK);

	return res;
}




#if !FF_FS_READONLY
/*-----------------------------------------------------------------------*/
/* Register an object to the directory                                   */
/*-----------------------------------------------------------------------*/

static FRESULT dir_register (	/* FR_OK:succeeded, FR_DENIED:no free entry or too many SFN collision, FR_DISK_ERR:disk error */
	DIR* dp						/* Target directory with object name to be created */
)
{
	FRESULT res;
	FATFS *fs = dp->obj.fs;
#if FF_USE_LFN		/* LFN configuration */
	UINT n, nlen, nent;
	BYTE sn[12], sum;


	if (dp->fn[NSFLAG] & (NS_DOT | NS_NONAME)) return FR_INVALID_NAME;	/* Check name validity */
	for (nlen = 0; fs->lfnbuf[nlen]; nlen++) ;	/* Get lfn length */

#if FF_FS_EXFAT
	if (fs->fs_type == FS_EXFAT) {	/* On the exFAT volume */
		nent = (nlen + 14) / 15 + 2;	/* Number of entries to allocate (85+C0+C1s) */
		res = dir_alloc(dp, nent);		/* Allocate entries */
		if (res != FR_OK) return res;
		dp->blk_ofs = dp->dptr - SZDIRE * (nent - 1);	/* Set the allocated entry block offset */

		if (dp->obj.stat & 4) {			/* Has the directory been stretched? */
			dp->obj.stat &= ~4;
			res = fill_first_frag(&dp->obj);	/* Fill the first fragment on the FAT if needed */
			if (res != FR_OK) return res;
			res = fill_last_frag(&dp->obj, dp->clust, 0xFFFFFFFF);	/* Fill the last fragment on the FAT if needed */
			if (res != FR_OK) return res;
			if (dp->obj.sclust != 0) {		/* Is it a sub directory? */
				DIR dj;

				res = load_obj_xdir(&dj, &dp->obj);	/* Load the object status */
				if (res != FR_OK) return res;
				dp->obj.objsize += (DWORD)fs->csize * SS(fs);			/* Increase the directory size by cluster size */
				st_qword(fs->dirbuf + XDIR_FileSize, dp->obj.objsize);	/* Update the allocation status */
				st_qword(fs->dirbuf + XDIR_ValidFileSize, dp->obj.objsize);
				fs->dirbuf[XDIR_GenFlags] = dp->obj.stat | 1;
				res = store_xdir(&dj);				/* Store the object status */
				if (res != FR_OK) return res;
			}
		}

		create_xdir(fs->dirbuf, fs->lfnbuf);	/* Create on-memory directory block to be written later */
		return FR_OK;
	}
#endif
	/* On the FAT/FAT32 volume */
	mem_cpy(sn, dp->fn, 12);
	if (sn[NSFLAG] & NS_LOSS) {			/* When LFN is out of 8.3 format, generate a numbered name */
		dp->fn[NSFLAG] = NS_NOLFN;		/* Find only SFN */
		for (n = 1; n < 100; n++) {
			gen_numname(dp->fn, sn, fs->lfnbuf, n);	/* Generate a numbered name */
			res = dir_find(dp);				/* Check if the name collides with existing SFN */
			if (res != FR_OK) break;
		}
		if (n == 100) return FR_DENIED;		/* Abort if too many collisions */
		if (res != FR_NO_FILE) return res;	/* Abort if the result is other than 'not collided' */
		dp->fn[NSFLAG] = sn[NSFLAG];
	}

	/* Create an SFN with/without LFNs. */
	nent = (sn[NSFLAG] & NS_LFN) ? (nlen + 12) / 13 + 1 : 1;	/* Number of entries to allocate */
	res = dir_alloc(dp, nent);		/* Allocate entries */
	if (res == FR_OK && --nent) {	/* Set LFN entry if needed */
		res = dir_sdi(dp, dp->dptr - nent * SZDIRE);
		if (res == FR_OK) {
			sum = sum_sfn(dp->fn);	/* Checksum value of the SFN tied to the LFN */
			do {					/* Store LFN entries in bottom first */
				res = move_window(fs, dp->sect);
				if (res != FR_OK) break;
				put_lfn(fs->lfnbuf, dp->dir, (BYTE)nent, sum);
				fs->wflag = 1;
				res = dir_next(dp, 0);	/* Next entry */
			} while (res == FR_OK && --nent);
		}
	}

#else	/* Non LFN configuration */
	res = dir_alloc(dp, 1);		/* Allocate an entry for SFN */

#endif

	/* Set SFN entry */
	if (res == FR_OK) {
		res = move_window(fs, dp->sect);
		if (res == FR_OK) {
			mem_set(dp->dir, 0, SZDIRE);	/* Clean the entry */
			mem_cpy(dp->dir + DIR_Name, dp->fn, 11);	/* Put SFN */
#if FF_USE_LFN
			dp->dir[DIR_NTres] = dp->fn[NSFLAG] & (NS_BODY | NS_EXT);	/* Put NT flag */
#endif
			fs->wflag = 1;
		}
	}

	return res;
}

#endif /* !FF_FS_READONLY */



#if !FF_FS_READONLY && FF_FS_MINIMIZE == 0
/*-----------------------------------------------------------------------*/
/* Remove an object from the directory                                   */
/*-----------------------------------------------------------------------*/

static FRESULT dir_remove (	/* FR_OK:Succeeded, FR_DISK_ERR:A disk error */
	DIR* dp					/* Directory object pointing the entry to be removed */
)
{
	FRESULT res;
	FATFS *fs = dp->obj.fs;
#if FF_USE_LFN		/* LFN configuration */
	DWORD last = dp->dptr;

	res = (dp->blk_ofs == 0xFFFFFFFF) ? FR_OK : dir_sdi(dp, dp->blk_ofs);	/* Goto top of the entry block if LFN is exist */
	if (res == FR_OK) {
		do {
			res = move_window(fs, dp->sect);
			if (res != FR_OK) break;
			if (FF_FS_EXFAT && fs->fs_type == FS_EXFAT) {	/* On the exFAT volume */
				dp->dir[XDIR_Type] &= 0x7F;	/* Clear the entry InUse flag. */
			} else {									/* On the FAT/FAT32 volume */
				dp->dir[DIR_Name] = DDEM;	/* Mark the entry 'deleted'. */
			}
			fs->wflag = 1;
			if (dp->dptr >= last) break;	/* If reached last entry then all entries of the object has been deleted. */
			res = dir_next(dp, 0);	/* Next entry */
		} while (res == FR_OK);
		if (res == FR_NO_FILE) res = FR_INT_ERR;
	}
#else			/* Non LFN configuration */

	res = move_window(fs, dp->sect);
	if (res == FR_OK) {
		dp->dir[DIR_Name] = DDEM;	/* Mark the entry 'deleted'.*/
		fs->wflag = 1;
	}
#endif

	return res;
}

#endif /* !FF_FS_READONLY && FF_FS_MINIMIZE == 0 */



#if FF_FS_MINIMIZE <= 1 || FF_FS_RPATH >= 2
/*-----------------------------------------------------------------------*/
/* Get file information from directory entry                             */
/*-----------------------------------------------------------------------*/

static void get_fileinfo (
	DIR* dp,			/* Pointer to the directory object */
	FILINFO* fno		/* Pointer to the file information to be filled */
)
{
	UINT si, di;
#if FF_USE_LFN
	WCHAR wc, hs;
	FATFS *fs = dp->obj.fs;
#else
	TCHAR c;
#endif


	fno->fname[0] = 0;			/* Invaidate file info */
	if (dp->sect == 0) return;	/* Exit if read pointer has reached end of directory */

#if FF_USE_LFN		/* LFN configuration */
#if FF_FS_EXFAT
	if (fs->fs_type == FS_EXFAT) {	/* On the exFAT volume */
		get_xfileinfo(fs->dirbuf, fno);
		return;
	} else
#endif
	{	/* On the FAT/FAT32 volume */
		if (dp->blk_ofs != 0xFFFFFFFF) {	/* Get LFN if available */
			si = di = hs = 0;
			while (fs->lfnbuf[si] != 0) {
				wc = fs->lfnbuf[si++];		/* Get an LFN character (UTF-16) */
				if (hs == 0 && IsSurrogate(wc)) {	/* Is it a surrogate? */
					hs = wc; continue;		/* Get low surrogate */
				}
				wc = put_utf((DWORD)hs << 16 | wc, &fno->fname[di], FF_LFN_BUF - di);	/* Store it in UTF-16 or UTF-8 encoding */
				if (wc == 0) { di = 0; break; }	/* Invalid char or buffer overflow? */
				di += wc;
				hs = 0;
			}
			if (hs != 0) di = 0;	/* Broken surrogate pair? */
			fno->fname[di] = 0;		/* Terminate the LFN (null string means LFN is invalid) */
		}
	}

	si = di = 0;
	while (si < 11) {		/* Get SFN from SFN entry */
		wc = dp->dir[si++];			/* Get a char */
		if (wc == ' ') continue;	/* Skip padding spaces */
		if (wc == RDDEM) wc = DDEM;	/* Restore replaced DDEM character */
		if (si == 9 && di < FF_SFN_BUF) fno->altname[di++] = '.';	/* Insert a . if extension is exist */
#if FF_LFN_UNICODE >= 1	/* Unicode output */
		if (dbc_1st((BYTE)wc) && si != 8 && si != 11 && dbc_2nd(dp->dir[si])) {	/* Make a DBC if needed */
			wc = wc << 8 | dp->dir[si++];
		}
		wc = ff_oem2uni(wc, CODEPAGE);		/* ANSI/OEM -> Unicode */
		if (wc == 0) { di = 0; break; }		/* Wrong char in the current code page? */
		wc = put_utf(wc, &fno->altname[di], FF_SFN_BUF - di);	/* Store it in Unicode */
		if (wc == 0) { di = 0; break; }		/* Buffer overflow? */
		di += wc;
#else					/* ANSI/OEM output */
		fno->altname[di++] = (TCHAR)wc;	/* Store it without any conversion */
#endif
	}
	fno->altname[di] = 0;	/* Terminate the SFN  (null string means SFN is invalid) */

	if (fno->fname[0] == 0) {	/* If LFN is invalid, altname[] needs to be copied to fname[] */
		if (di == 0) {	/* If LFN and SFN both are invalid, this object is inaccesible */
			fno->fname[di++] = '?';
		} else {
			for (si = di = 0; fno->altname[si]; si++, di++) {	/* Copy altname[] to fname[] with case information */
				wc = (WCHAR)fno->altname[si];
				if (IsUpper(wc) && (dp->dir[DIR_NTres] & ((si >= 9) ? NS_EXT : NS_BODY))) wc += 0x20;
				fno->fname[di] = (TCHAR)wc;
			}
		}
		fno->fname[di] = 0;	/* Terminate the LFN */
		if (!dp->dir[DIR_NTres]) fno->altname[0] = 0;	/* Altname is not needed if neither LFN nor case info is exist. */
	}

#else	/* Non-LFN configuration */
	si = di = 0;
	while (si < 11) {		/* Copy name body and extension */
		c = (TCHAR)dp->dir[si++];
		if (c == ' ') continue;		/* Skip padding spaces */
		if (c == RDDEM) c = DDEM;	/* Restore replaced DDEM character */
		if (si == 9) fno->fname[di++] = '.';/* Insert a . if extension is exist */
		fno->fname[di++] = c;
	}
	fno->fname[di] = 0;
#endif

	fno->fattrib = dp->dir[DIR_Attr];					/* Attribute */
	fno->fsize = ld_dword(dp->dir + DIR_FileSize);		/* Size */
	fno->ftime = ld_word(dp->dir + DIR_ModTime + 0);	/* Time */
	fno->fdate = ld_word(dp->dir + DIR_ModTime + 2);	/* Date */
}

#endif /* FF_FS_MINIMIZE <= 1 || FF_FS_RPATH >= 2 */



#if FF_USE_FIND && FF_FS_MINIMIZE <= 1
/*-----------------------------------------------------------------------*/
/* Pattern matching                                                      */
/*-----------------------------------------------------------------------*/

static DWORD get_achar (	/* Get a character and advances ptr */
	const TCHAR** ptr		/* Pointer to pointer to the ANSI/OEM or Unicode string */
)
{
	DWORD chr;


#if FF_USE_LFN && FF_LFN_UNICODE >= 1	/* Unicode input */
	chr = tchar2uni(ptr);
	if (chr == 0xFFFFFFFF) chr = 0;		/* Wrong UTF encoding is recognized as end of the string */
	chr = ff_wtoupper(chr);

#else									/* ANSI/OEM input */
	chr = (BYTE)*(*ptr)++;				/* Get a byte */
	if (IsLower(chr)) chr -= 0x20;		/* To upper ASCII char */
#if FF_CODE_PAGE == 0
	if (ExCvt && chr >= 0x80) chr = ExCvt[chr - 0x80];	/* To upper SBCS extended char */
#elif FF_CODE_PAGE < 900
	if (chr >= 0x80) chr = ExCvt[chr - 0x80];	/* To upper SBCS extended char */
#endif
#if FF_CODE_PAGE == 0 || FF_CODE_PAGE >= 900
	if (dbc_1st((BYTE)chr)) {	/* Get DBC 2nd byte if needed */
		chr = dbc_2nd((BYTE)**ptr) ? chr << 8 | (BYTE)*(*ptr)++ : 0;
	}
#endif

#endif
	return chr;
}


static int pattern_matching (	/* 0:not matched, 1:matched */
	const TCHAR* pat,	/* Matching pattern */
	const TCHAR* nam,	/* String to be tested */
	int skip,			/* Number of pre-skip chars (number of ?s) */
	int inf				/* Infinite search (* specified) */
)
{
	const TCHAR *pp, *np;
	DWORD pc, nc;
	int nm, nx;


	while (skip--) {				/* Pre-skip name chars */
		if (!get_achar(&nam)) return 0;	/* Branch mismatched if less name chars */
	}
	if (*pat == 0 && inf) return 1;	/* (short circuit) */

	do {
		pp = pat; np = nam;			/* Top of pattern and name to match */
		for (;;) {
			if (*pp == '?' || *pp == '*') {	/* Wildcard? */
				nm = nx = 0;
				do {				/* Analyze the wildcard block */
					if (*pp++ == '?') nm++; else nx = 1;
				} while (*pp == '?' || *pp == '*');
				if (pattern_matching(pp, np, nm, nx)) return 1;	/* Test new branch (recurs upto number of wildcard blocks in the pattern) */
				nc = *np; break;	/* Branch mismatched */
			}
			pc = get_achar(&pp);	/* Get a pattern char */
			nc = get_achar(&np);	/* Get a name char */
			if (pc != nc) break;	/* Branch mismatched? */
			if (pc == 0) return 1;	/* Branch matched? (matched at end of both strings) */
		}
		get_achar(&nam);			/* nam++ */
	} while (inf && nc);			/* Retry until end of name if infinite search is specified */

	return 0;
}

#endif /* FF_USE_FIND && FF_FS_MINIMIZE <= 1 */



/*-----------------------------------------------------------------------*/
/* Pick a top segment and create the object name in directory form       */
/*-----------------------------------------------------------------------*/

static FRESULT create_name (	/* FR_OK: successful, FR_INVALID_NAME: could not create */
	DIR* dp,					/* Pointer to the directory object */
	const TCHAR** path			/* Pointer to pointer to the segment in the path string */
)
{
#if FF_USE_LFN		/* LFN configuration */
	BYTE b, cf;
	WCHAR wc, *lfn;
	DWORD uc;
	UINT i, ni, si, di;
	const TCHAR *p;


	/* Create LFN into LFN working buffer */
	p = *path; lfn = dp->obj.fs->lfnbuf; di = 0;
	for (;;) {
		uc = tchar2uni(&p);			/* Get a character */
		if (uc == 0xFFFFFFFF) return FR_INVALID_NAME;		/* Invalid code or UTF decode error */
		if (uc >= 0x10000) lfn[di++] = (WCHAR)(uc >> 16);	/* Store high surrogate if needed */
		wc = (WCHAR)uc;
		if (wc < ' ' || wc == '/' || wc == '\\') break;	/* Break if end of the path or a separator is found */
		if (wc < 0x80 && chk_chr("\"*:<>\?|\x7F", wc)) return FR_INVALID_NAME;	/* Reject illegal characters for LFN */
		if (di >= FF_MAX_LFN) return FR_INVALID_NAME;	/* Reject too long name */
		lfn[di++] = wc;					/* Store the Unicode character */
	}
	while (*p == '/' || *p == '\\') p++;	/* Skip duplicated separators if exist */
	*path = p;							/* Return pointer to the next segment */
	cf = (wc < ' ') ? NS_LAST : 0;		/* Set last segment flag if end of the path */

#if FF_FS_RPATH != 0
	if ((di == 1 && lfn[di - 1] == '.') ||
		(di == 2 && lfn[di - 1] == '.' && lfn[di - 2] == '.')) {	/* Is this segment a dot name? */
		lfn[di] = 0;
		for (i = 0; i < 11; i++) {		/* Create dot name for SFN entry */
			dp->fn[i] = (i < di) ? '.' : ' ';
		}
		dp->fn[i] = cf | NS_DOT;		/* This is a dot entry */
		return FR_OK;
	}
#endif
	while (di) {						/* Snip off trailing spaces and dots if exist */
		wc = lfn[di - 1];
		if (wc != ' ' && wc != '.') break;
		di--;
	}
	lfn[di] = 0;							/* LFN is created into the working buffer */
	if (di == 0) return FR_INVALID_NAME;	/* Reject null name */

	/* Create SFN in directory form */
	for (si = 0; lfn[si] == ' '; si++) ;	/* Remove leading spaces */
	if (si > 0 || lfn[si] == '.') cf |= NS_LOSS | NS_LFN;	/* Is there any leading space or dot? */
	while (di > 0 && lfn[di - 1] != '.') di--;	/* Find last dot (di<=si: no extension) */

	mem_set(dp->fn, ' ', 11);
	i = b = 0; ni = 8;
	for (;;) {
		wc = lfn[si++];					/* Get an LFN character */
		if (wc == 0) break;				/* Break on end of the LFN */
		if (wc == ' ' || (wc == '.' && si != di)) {	/* Remove embedded spaces and dots */
			cf |= NS_LOSS | NS_LFN;
			continue;
		}

		if (i >= ni || si == di) {		/* End of field? */
			if (ni == 11) {				/* Name extension overflow? */
				cf |= NS_LOSS | NS_LFN;
				break;
			}
			if (si != di) cf |= NS_LOSS | NS_LFN;	/* Name body overflow? */
			if (si > di) break;						/* No name extension? */
			si = di; i = 8; ni = 11; b <<= 2;		/* Enter name extension */
			continue;
		}

		if (wc >= 0x80) {	/* Is this a non-ASCII character? */
			cf |= NS_LFN;	/* LFN entry needs to be created */
#if FF_CODE_PAGE == 0
			if (ExCvt) {	/* At SBCS */
				wc = ff_uni2oem(wc, CODEPAGE);			/* Unicode ==> ANSI/OEM code */
				if (wc & 0x80) wc = ExCvt[wc & 0x7F];	/* Convert extended character to upper (SBCS) */
			} else {		/* At DBCS */
				wc = ff_uni2oem(ff_wtoupper(wc), CODEPAGE);	/* Unicode ==> Upper convert ==> ANSI/OEM code */
			}
#elif FF_CODE_PAGE < 900	/* SBCS cfg */
			wc = ff_uni2oem(wc, CODEPAGE);			/* Unicode ==> ANSI/OEM code */
			if (wc & 0x80) wc = ExCvt[wc & 0x7F];	/* Convert extended character to upper (SBCS) */
#else						/* DBCS cfg */
			wc = ff_uni2oem(ff_wtoupper(wc), CODEPAGE);	/* Unicode ==> Upper convert ==> ANSI/OEM code */
#endif
		}

		if (wc >= 0x100) {				/* Is this a DBC? */
			if (i >= ni - 1) {			/* Field overflow? */
				cf |= NS_LOSS | NS_LFN;
				i = ni; continue;		/* Next field */
			}
			dp->fn[i++] = (BYTE)(wc >> 8);	/* Put 1st byte */
		} else {						/* SBC */
			if (wc == 0 || chk_chr("+,;=[]", wc)) {	/* Replace illegal characters for SFN if needed */
				wc = '_'; cf |= NS_LOSS | NS_LFN;/* Lossy conversion */
			} else {
				if (IsUpper(wc)) {		/* ASCII upper case? */
					b |= 2;
				}
				if (IsLower(wc)) {		/* ASCII lower case? */
					b |= 1; wc -= 0x20;
				}
			}
		}
		dp->fn[i++] = (BYTE)wc;
	}

	if (dp->fn[0] == DDEM) dp->fn[0] = RDDEM;	/* If the first character collides with DDEM, replace it with RDDEM */

	if (ni == 8) b <<= 2;				/* Shift capital flags if no extension */
	if ((b & 0x0C) == 0x0C || (b & 0x03) == 0x03) cf |= NS_LFN;	/* LFN entry needs to be created if composite capitals */
	if (!(cf & NS_LFN)) {				/* When LFN is in 8.3 format without extended character, NT flags are created */
		if (b & 0x01) cf |= NS_EXT;		/* NT flag (Extension has small capital letters only) */
		if (b & 0x04) cf |= NS_BODY;	/* NT flag (Body has small capital letters only) */
	}

	dp->fn[NSFLAG] = cf;	/* SFN is created into dp->fn[] */

	return FR_OK;


#else	/* FF_USE_LFN : Non-LFN configuration */
	BYTE c, d, *sfn;
	UINT ni, si, i;
	const char *p;

	/* Create file name in directory form */
	p = *path; sfn = dp->fn;
	mem_set(sfn, ' ', 11);
	si = i = 0; ni = 8;
#if FF_FS_RPATH != 0
	if (p[si] == '.') { /* Is this a dot entry? */
		for (;;) {
			c = (BYTE)p[si++];
			if (c != '.' || si >= 3) break;
			sfn[i++] = c;
		}
		if (c != '/' && c != '\\' && c > ' ') return FR_INVALID_NAME;
		*path = p + si;								/* Return pointer to the next segment */
		sfn[NSFLAG] = (c <= ' ') ? NS_LAST | NS_DOT : NS_DOT;	/* Set last segment flag if end of the path */
		return FR_OK;
	}
#endif
	for (;;) {
		c = (BYTE)p[si++];				/* Get a byte */
		if (c <= ' ') break; 			/* Break if end of the path name */
		if (c == '/' || c == '\\') {	/* Break if a separator is found */
			while (p[si] == '/' || p[si] == '\\') si++;	/* Skip duplicated separator if exist */
			break;
		}
		if (c == '.' || i >= ni) {		/* End of body or field overflow? */
			if (ni == 11 || c != '.') return FR_INVALID_NAME;	/* Field overflow or invalid dot? */
			i = 8; ni = 11;				/* Enter file extension field */
			continue;
		}
#if FF_CODE_PAGE == 0
		if (ExCvt && c >= 0x80) {		/* Is SBC extended character? */
			c = ExCvt[c & 0x7F];		/* To upper SBC extended character */
		}
#elif FF_CODE_PAGE < 900
		if (c >= 0x80) {				/* Is SBC extended character? */
			c = ExCvt[c & 0x7F];		/* To upper SBC extended character */
		}
#endif
		if (dbc_1st(c)) {				/* Check if it is a DBC 1st byte */
			d = (BYTE)p[si++];			/* Get 2nd byte */
			if (!dbc_2nd(d) || i >= ni - 1) return FR_INVALID_NAME;	/* Reject invalid DBC */
			sfn[i++] = c;
			sfn[i++] = d;
		} else {						/* SBC */
			if (chk_chr("\"*+,:;<=>\?[]|\x7F", c)) return FR_INVALID_NAME;	/* Reject illegal chrs for SFN */
			if (IsLower(c)) c -= 0x20;	/* To upper */
			sfn[i++] = c;
		}
	}
	*path = p + si;						/* Return pointer to the next segment */
	if (i == 0) return FR_INVALID_NAME;	/* Reject nul string */

	if (sfn[0] == DDEM) sfn[0] = RDDEM;	/* If the first character collides with DDEM, replace it with RDDEM */
	sfn[NSFLAG] = (c <= ' ') ? NS_LAST : 0;		/* Set last segment flag if end of the path */

	return FR_OK;
#endif /* FF_USE_LFN */
}




/*-----------------------------------------------------------------------*/
/* Follow a file path                                                    */
/*-----------------------------------------------------------------------*/

static FRESULT follow_path (	/* FR_OK(0): successful, !=0: error code */
	DIR* dp,					/* Directory object to return last directory and found object */
	const TCHAR* path			/* Full-path string to find a file or directory */
)
{
	FRESULT res;
	BYTE ns;
	FATFS *fs = dp->obj.fs;


#if FF_FS_RPATH != 0
	if (*path != '/' && *path != '\\') {	/* Without heading separator */
		dp->obj.sclust = fs->cdir;				/* Start from current directory */
	} else
#endif
	{										/* With heading separator */
		while (*path == '/' || *path == '\\') path++;	/* Strip heading separator */
		dp->obj.sclust = 0;					/* Start from root directory */
	}
#if FF_FS_EXFAT
	dp->obj.n_frag = 0;	/* Invalidate last fragment counter of the object */
#if FF_FS_RPATH != 0
	if (fs->fs_type == FS_EXFAT && dp->obj.sclust) {	/* exFAT: Retrieve the sub-directory's status */
		DIR dj;

		dp->obj.c_scl = fs->cdc_scl;
		dp->obj.c_size = fs->cdc_size;
		dp->obj.c_ofs = fs->cdc_ofs;
		res = load_obj_xdir(&dj, &dp->obj);
		if (res != FR_OK) return res;
		dp->obj.objsize = ld_dword(fs->dirbuf + XDIR_FileSize);
		dp->obj.stat = fs->dirbuf[XDIR_GenFlags] & 2;
	}
#endif
#endif

	if ((UINT)*path < ' ') {				/* Null path name is the origin directory itself */
		dp->fn[NSFLAG] = NS_NONAME;
		res = dir_sdi(dp, 0);

	} else {								/* Follow path */
		for (;;) {
			res = create_name(dp, &path);	/* Get a segment name of the path */
			if (res != FR_OK) break;
			res = dir_find(dp);				/* Find an object with the segment name */
			ns = dp->fn[NSFLAG];
			if (res != FR_OK) {				/* Failed to find the object */
				if (res == FR_NO_FILE) {	/* Object is not found */
					if (FF_FS_RPATH && (ns & NS_DOT)) {	/* If dot entry is not exist, stay there */
						if (!(ns & NS_LAST)) continue;	/* Continue to follow if not last segment */
						dp->fn[NSFLAG] = NS_NONAME;
						res = FR_OK;
					} else {							/* Could not find the object */
						if (!(ns & NS_LAST)) res = FR_NO_PATH;	/* Adjust error code if not last segment */
					}
				}
				break;
			}
			if (ns & NS_LAST) break;			/* Last segment matched. Function completed. */
			/* Get into the sub-directory */
			if (!(dp->obj.attr & AM_DIR)) {		/* It is not a sub-directory and cannot follow */
				res = FR_NO_PATH; break;
			}
#if FF_FS_EXFAT
			if (fs->fs_type == FS_EXFAT) {		/* Save containing directory information for next dir */
				dp->obj.c_scl = dp->obj.sclust;
				dp->obj.c_size = ((DWORD)dp->obj.objsize & 0xFFFFFF00) | dp->obj.stat;
				dp->obj.c_ofs = dp->blk_ofs;
				init_alloc_info(fs, &dp->obj);	/* Open next directory */
			} else
#endif
			{
				dp->obj.sclust = ld_clust(fs, fs->win + dp->dptr % SS(fs));	/* Open next directory */
			}
		}
	}

	return res;
}




/*-----------------------------------------------------------------------*/
/* Get logical drive number from path name                               */
/*-----------------------------------------------------------------------*/

static int get_ldnumber (	/* Returns logical drive number (-1:invalid drive number or null pointer) */
	const TCHAR** path		/* Pointer to pointer to the path name */
)
{
	const TCHAR *tp, *tt;
	TCHAR tc;
	int i, vol = -1;
#if FF_STR_VOLUME_ID		/* Find string volume ID */
	const char *sp;
	char c;
#endif

	tt = tp = *path;
	if (!tp) return vol;	/* Invalid path name? */
	do tc = *tt++; while ((UINT)tc >= (FF_USE_LFN ? ' ' : '!') && tc != ':');	/* Find a colon in the path */

	if (tc == ':') {	/* DOS/Windows style volume ID? */
		i = FF_VOLUMES;
		if (IsDigit(*tp) && tp + 2 == tt) {	/* Is there a numeric volume ID + colon? */
			i = (int)*tp - '0';	/* Get the LD number */
		}
#if FF_STR_VOLUME_ID == 1	/* Arbitrary string is enabled */
		else {
			i = 0;
			do {
				sp = VolumeStr[i]; tp = *path;	/* This string volume ID and path name */
				do {	/* Compare the volume ID with path name */
					c = *sp++; tc = *tp++;
					if (IsLower(c)) c -= 0x20;
					if (IsLower(tc)) tc -= 0x20;
				} while (c && (TCHAR)c == tc);
			} while ((c || tp != tt) && ++i < FF_VOLUMES);	/* Repeat for each id until pattern match */
		}
#endif
		if (i < FF_VOLUMES) {	/* If a volume ID is found, get the drive number and strip it */
			vol = i;		/* Drive number */
			*path = tt;		/* Snip the drive prefix off */
		}
		return vol;
	}
#if FF_STR_VOLUME_ID == 2		/* Unix style volume ID is enabled */
	if (*tp == '/') {
		i = 0;
		do {
			sp = VolumeStr[i]; tp = *path;	/* This string volume ID and path name */
			do {	/* Compare the volume ID with path name */
				c = *sp++; tc = *(++tp);
				if (IsLower(c)) c -= 0x20;
				if (IsLower(tc)) tc -= 0x20;
			} while (c && (TCHAR)c == tc);
		} while ((c || (tc != '/' && (UINT)tc >= (FF_USE_LFN ? ' ' : '!'))) && ++i < FF_VOLUMES);	/* Repeat for each ID until pattern match */
		if (i < FF_VOLUMES) {	/* If a volume ID is found, get the drive number and strip it */
			vol = i;		/* Drive number */
			*path = tp;		/* Snip the drive prefix off */
			return vol;
		}
	}
#endif
	/* No drive prefix is found */
#if FF_FS_RPATH != 0
	vol = CurrVol;	/* Default drive is current drive */
#else
	vol = 0;		/* Default drive is 0 */
#endif
	return vol;		/* Return the default drive */
}




/*-----------------------------------------------------------------------*/
/* Load a sector and check if it is an FAT VBR                           */
/*-----------------------------------------------------------------------*/

static BYTE check_fs (	/* 0:FAT, 1:exFAT, 2:Valid BS but not FAT, 3:Not a BS, 4:Disk error */
	FATFS* fs,			/* Filesystem object */
	DWORD sect			/* Sector# (lba) to load and check if it is an FAT-VBR or not */
)
{
	fs->wflag = 0; fs->winsect = 0xFFFFFFFF;		/* Invaidate window */
	if (move_window(fs, sect) != FR_OK) return 4;	/* Load boot record */

	if (ld_word(fs->win + BS_55AA) != 0xAA55) return 3;	/* Check boot record signature (always here regardless of the sector size) */

#if FF_FS_EXFAT
	if (!mem_cmp(fs->win + BS_JmpBoot, "\xEB\x76\x90" "EXFAT   ", 11)) return 1;	/* Check if exFAT VBR */
#endif
	if (fs->win[BS_JmpBoot] == 0xE9 || fs->win[BS_JmpBoot] == 0xEB || fs->win[BS_JmpBoot] == 0xE8) {	/* Valid JumpBoot code? */
		if (!mem_cmp(fs->win + BS_FilSysType, "FAT", 3)) return 0;		/* Is it an FAT VBR? */
		if (!mem_cmp(fs->win + BS_FilSysType32, "FAT32", 5)) return 0;	/* Is it an FAT32 VBR? */
	}
	return 2;	/* Valid BS but not FAT */
}




/*-----------------------------------------------------------------------*/
/* Determine logical drive number and mount the volume if needed         */
/*-----------------------------------------------------------------------*/

static FRESULT find_volume (	/* FR_OK(0): successful, !=0: an error occurred */
	const TCHAR** path,			/* Pointer to pointer to the path name (drive number) */
	FATFS** rfs,				/* Pointer to pointer to the found filesystem object */
	BYTE mode					/* !=0: Check write protection for write access */
)
{
	BYTE fmt, *pt;
	int vol;
	DSTATUS stat;
	DWORD bsect, fasize, tsect, sysect, nclst, szbfat, br[4];
	WORD nrsv;
	FATFS *fs;
	UINT i;


	/* Get logical drive number */
	*rfs = 0;
	vol = get_ldnumber(path);
	if (vol < 0) return FR_INVALID_DRIVE;

	/* Check if the filesystem object is valid or not */
	fs = FatFs[vol];					/* Get pointer to the filesystem object */
	if (!fs) return FR_NOT_ENABLED;		/* Is the filesystem object available? */
#if FF_FS_REENTRANT
	if (!lock_fs(fs)) return FR_TIMEOUT;	/* Lock the volume */
#endif
	*rfs = fs;							/* Return pointer to the filesystem object */

	mode &= (BYTE)~FA_READ;				/* Desired access mode, write access or not */
	if (fs->fs_type != 0) {				/* If the volume has been mounted */
		stat = disk_status(fs->pdrv);
		if (!(stat & STA_NOINIT)) {		/* and the physical drive is kept initialized */
			if (!FF_FS_READONLY && mode && (stat & STA_PROTECT)) {	/* Check write protection if needed */
				return FR_WRITE_PROTECTED;
			}
			return FR_OK;				/* The filesystem object is valid */
		}
	}

	/* The filesystem object is not valid. */
	/* Following code attempts to mount the volume. (analyze BPB and initialize the filesystem object) */

	fs->fs_type = 0;					/* Clear the filesystem object */
	fs->pdrv = LD2PD(vol);				/* Bind the logical drive and a physical drive */
	stat = disk_initialize(fs->pdrv);	/* Initialize the physical drive */
	if (stat & STA_NOINIT) { 			/* Check if the initialization succeeded */
		return FR_NOT_READY;			/* Failed to initialize due to no medium or hard error */
	}
	if (!FF_FS_READONLY && mode && (stat & STA_PROTECT)) { /* Check disk write protection if needed */
		return FR_WRITE_PROTECTED;
	}
#if FF_MAX_SS != FF_MIN_SS				/* Get sector size (multiple sector size cfg only) */
	if (disk_ioctl(fs->pdrv, GET_SECTOR_SIZE, &SS(fs)) != RES_OK) return FR_DISK_ERR;
	if (SS(fs) > FF_MAX_SS || SS(fs) < FF_MIN_SS || (SS(fs) & (SS(fs) - 1))) return FR_DISK_ERR;
#endif

	/* Find an FAT partition on the drive. Supports only generic partitioning rules, FDISK and SFD. */
	bsect = 0;
	fmt = check_fs(fs, bsect);			/* Load sector 0 and check if it is an FAT-VBR as SFD */
	if (fmt == 2 || (fmt < 2 && LD2PT(vol) != 0)) {	/* Not an FAT-VBR or forced partition number */
		for (i = 0; i < 4; i++) {		/* Get partition offset */
			pt = fs->win + (MBR_Table + i * SZ_PTE);
			br[i] = pt[PTE_System] ? ld_dword(pt + PTE_StLba) : 0;
		}
		i = LD2PT(vol);					/* Partition number: 0:auto, 1-4:forced */
		if (i != 0) i--;
		do {							/* Find an FAT volume */
			bsect = br[i];
			fmt = bsect ? check_fs(fs, bsect) : 3;	/* Check the partition */
		} while (LD2PT(vol) == 0 && fmt >= 2 && ++i < 4);
	}
	if (fmt == 4) return FR_DISK_ERR;		/* An error occured in the disk I/O layer */
	if (fmt >= 2) return FR_NO_FILESYSTEM;	/* No FAT volume is found */

	/* An FAT volume is found (bsect). Following code initializes the filesystem object */
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
