Occator/DripMatic/src/atexit.cpp

/* Copyright (c) 2013  Embecosm
   All rights reserved.
   Redistribution and use in source and binary forms, with or without
   modification, are permitted provided that the following conditions are met:
   * Redistributions of source code must retain the above copyright
     notice, this list of conditions and the following disclaimer.
   * Redistributions in binary form must reproduce the above copyright
     notice, this list of conditions and the following disclaimer in
     the documentation and/or other materials provided with the
     distribution.
   * Neither the name of the copyright holders nor the names of
     contributors may be used to endorse or promote products derived
     from this software without specific prior written permission.
   THIS SOFTWARE IS PROVIDED BY THE COPYRIGHT HOLDERS AND CONTRIBUTORS "AS IS"
   AND ANY EXPRESS OR IMPLIED WARRANTIES, INCLUDING, BUT NOT LIMITED TO, THE
   IMPLIED WARRANTIES OF MERCHANTABILITY AND FITNESS FOR A PARTICULAR PURPOSE
   ARE DISCLAIMED. IN NO EVENT SHALL THE COPYRIGHT OWNER OR CONTRIBUTORS BE
   LIABLE FOR ANY DIRECT, INDIRECT, INCIDENTAL, SPECIAL, EXEMPLARY, OR
   CONSEQUENTIAL DAMAGES (INCLUDING, BUT NOT LIMITED TO, PROCUREMENT OF
   SUBSTITUTE GOODS OR SERVICES; LOSS OF USE, DATA, OR PROFITS; OR BUSINESS
   INTERRUPTION) HOWEVER CAUSED AND ON ANY THEORY OF LIABILITY, WHETHER IN
   CONTRACT, STRICT LIABILITY, OR TORT (INCLUDING NEGLIGENCE OR OTHERWISE)
   ARISING IN ANY WAY OUT OF THE USE OF THIS SOFTWARE, EVEN IF ADVISED OF THE
   POSSIBILITY OF SUCH DAMAGE. */

/*NOTE: follow change needs to be made in avr/stdlib.h
        line 675 - set value to 1*/

#include <stdlib.h>

struct atexit_s { void (*fun) (void); struct atexit_s *next; } *__atexit_p;

int
atexit (void (*fun) (void))
{
  struct atexit_s *new_as = (struct atexit_s *) malloc (sizeof *new_as);
  if (!new_as)
    return 1;
  new_as->fun = fun;
  new_as->next = __atexit_p;
  __atexit_p = new_as;
  return 0;
}

void __attribute__((section(".fini6a")))
__atexit_fini (void)
{
  while (__atexit_p)
    {
      void (*fun) (void) = __atexit_p->fun;
      __atexit_p = __atexit_p->next;
      (*fun) ();
    }
}
