Occator/DripMatic/include/twi_module.h

#ifndef CLASS_TWI_H
#define CLASS_TWI_H

#include <avr/io.h>
#include <stdint.h>
#include <stdlib.h>

#define F_CPU 16000000UL
#define S_CLK 400000UL
#define TWBR_VALUE ( ( (F_CPU / S_CLK) - 16) / 2)

// status-codes for Master Transmit Mode (MT-Mode)
#define TWI_START 0x08U
#define SLA_W_ACK 0x18U
#define SLA_W_NACK 0x20U
#define DATA_ACK 0x28U
#define DATA_NACK 0x30U

class cTWI{
public:
	cTWI(uint8_t devAddress);
	~cTWI();

	void init();
	void transmit(uint8_t data);
	uint8_t receive()	;
private:
	void start();
	void stop();
	void write(uint8_t data);
	uint8_t read();

	uint8_t _devAddr;
};

#endif
